3pnguyen/lionstride-inventeam-2026/Finalized Schematics/Finalized Pressure Schematic/Schematic Versions/Schematic V02/V2.2 - 5.3.2026/Pressure Schematic PCB.png

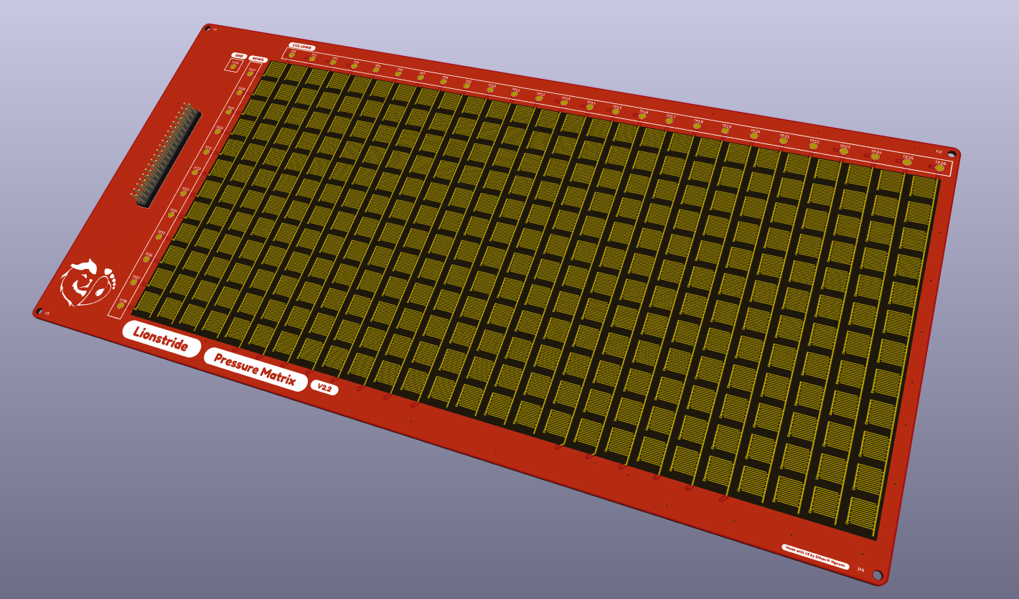
Finalized Schematics/Finalized Pressure Schematic/Schematic Versions/Schematic V02/V2.2 - 5.3.2026/Pressure Schematic PCB.png
