3pnguyen/lionstride-inventeam-2026/Finalized Schematics/Finalized Logic Schematic/Schematic Versions/Schematic V03/Logic Schematic.png

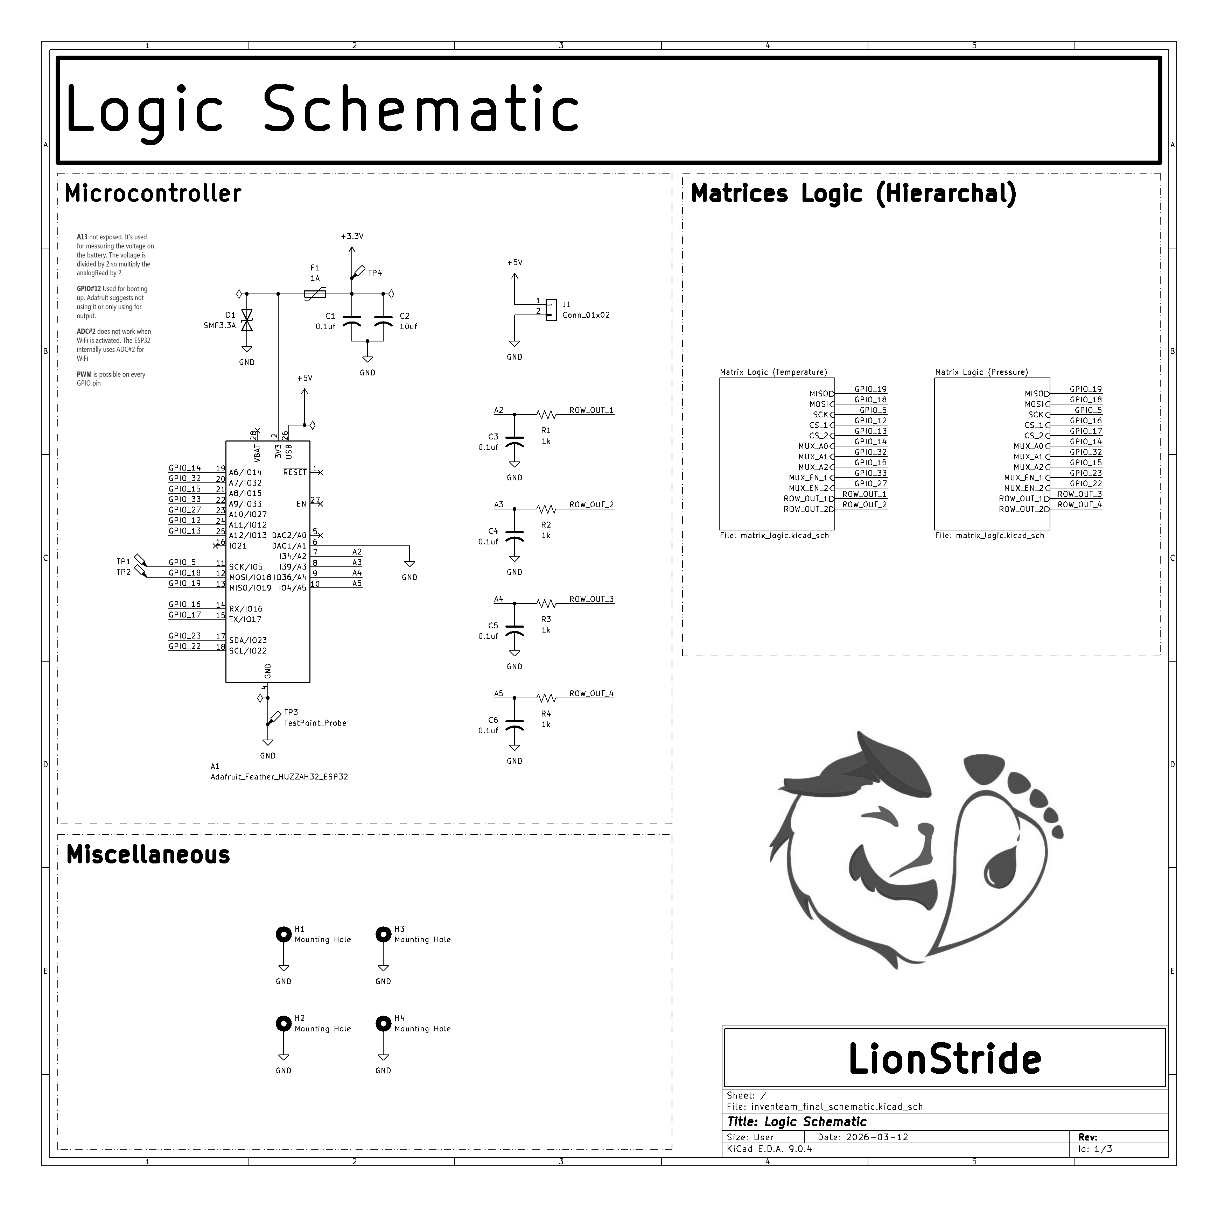
Finalized Schematics/Finalized Logic Schematic/Schematic Versions/Schematic V03/Logic Schematic.png
