3pnguyen/lionstride-inventeam-2026/Finalized Schematics/Finalized Logic Schematic/Schematic Versions/Schematic V03/Pressure Logic Subsheet.png

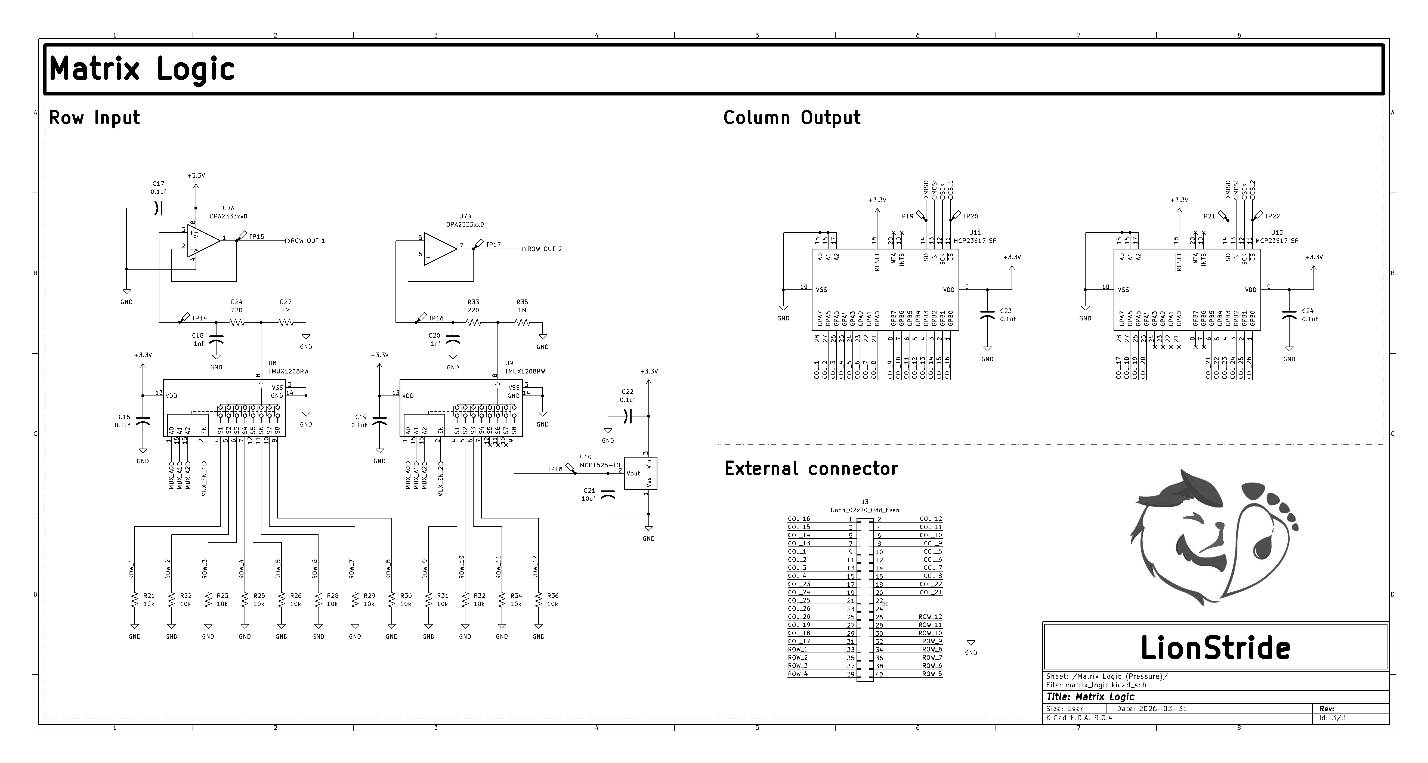
Finalized Schematics/Finalized Logic Schematic/Schematic Versions/Schematic V03/Pressure Logic Subsheet.png
