3pnguyen/lionstride-inventeam-2026/Finalized Schematics/Finalized Pressure Schematic/Schematic Versions/Schematic V02/Columns Hierarchical Schematic.png

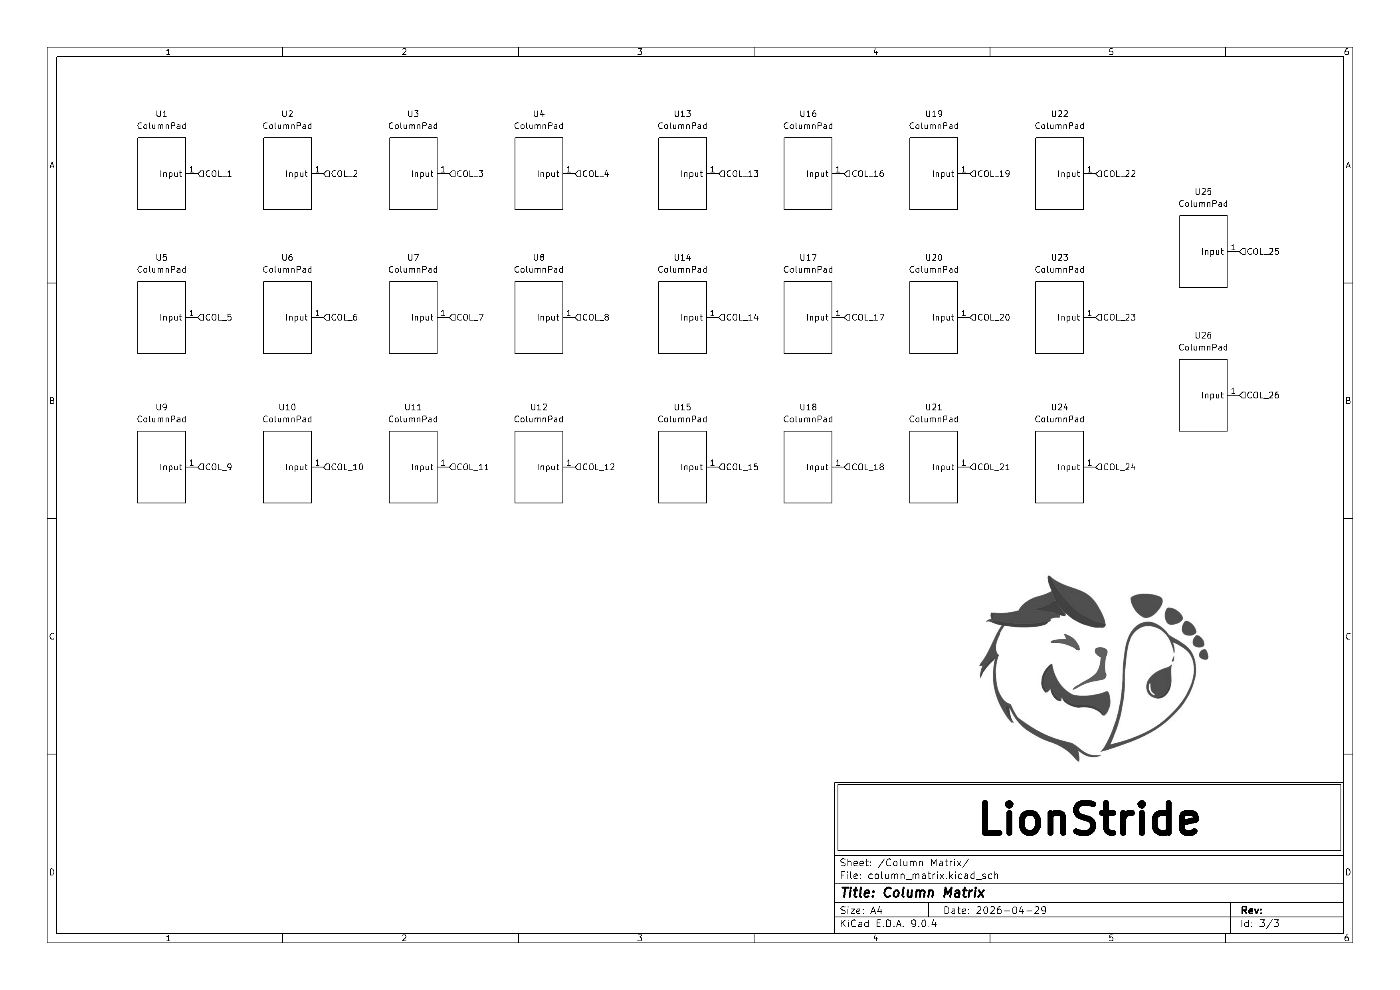
Finalized Schematics/Finalized Pressure Schematic/Schematic Versions/Schematic V02/Columns Hierarchical Schematic.png
