3pnguyen/lionstride-inventeam-2026/Finalized Schematics/Finalized Pressure Schematic/Schematic Versions/Schematic V02/V2.1 - 5.2.26/Pressure Schematic.png

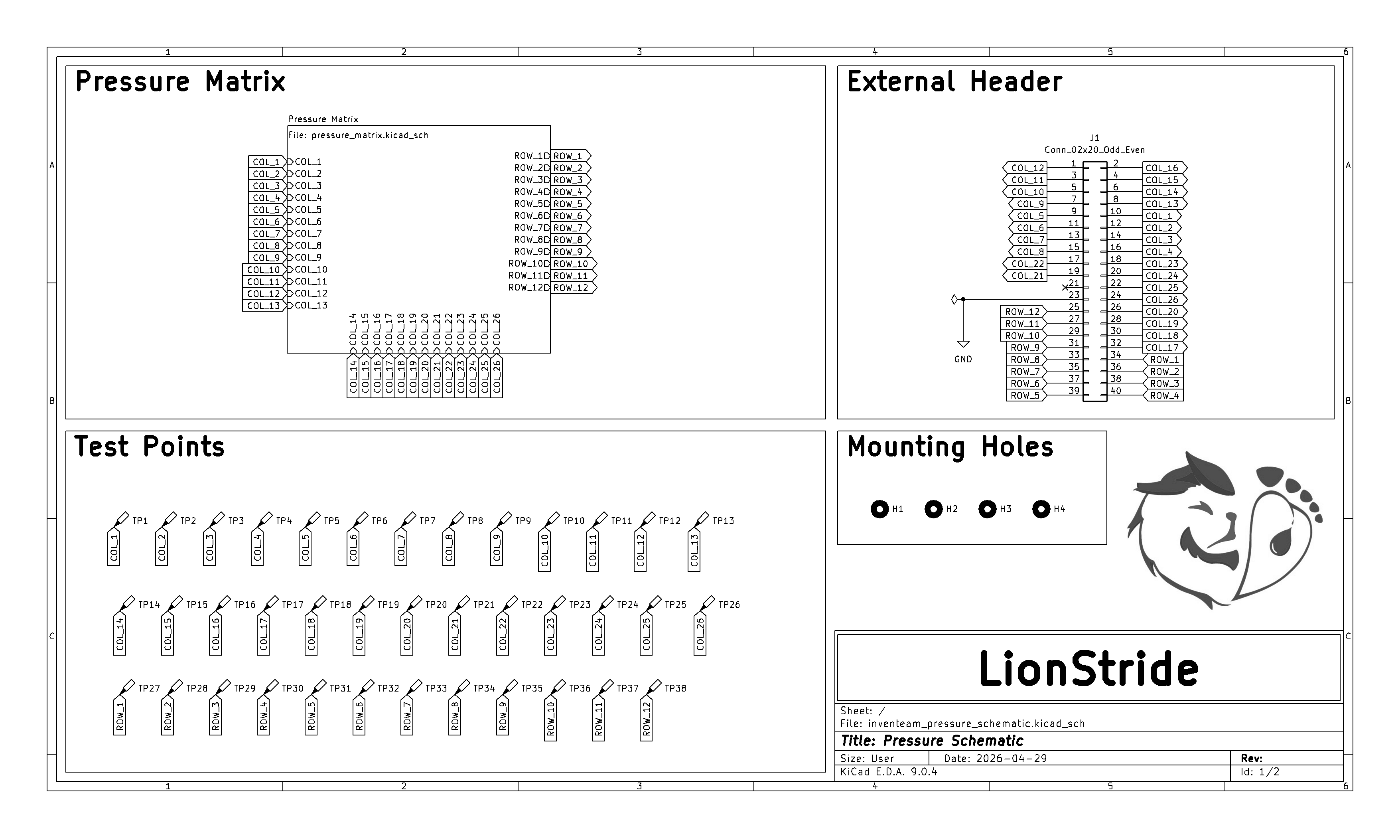
Finalized Schematics/Finalized Pressure Schematic/Schematic Versions/Schematic V02/V2.1 - 5.2.26/Pressure Schematic.png
