3pnguyen/lionstride-inventeam-2026/Finalized Schematics/Finalized Thermistor Schematic/Schematic Versions/Schematic V02/Matrix PCB Layout 2.png

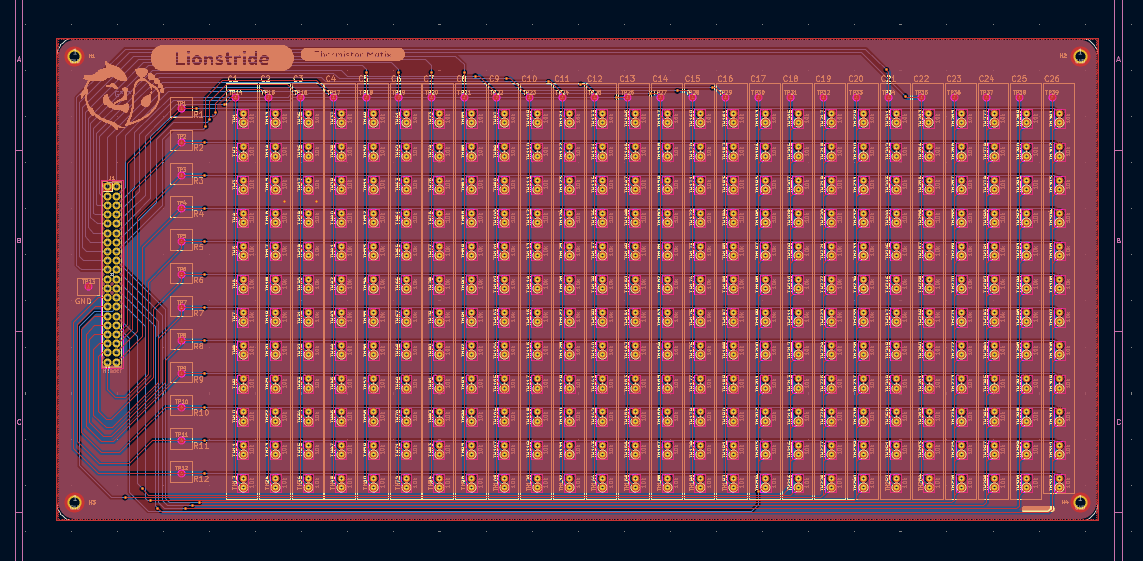
Finalized Schematics/Finalized Thermistor Schematic/Schematic Versions/Schematic V02/Matrix PCB Layout 2.png
