3pnguyen/lionstride-inventeam-2026/Finalized Schematics/Finalized Thermistor Schematic/Schematic Versions/Schematic V02/Thermistor Cell.png

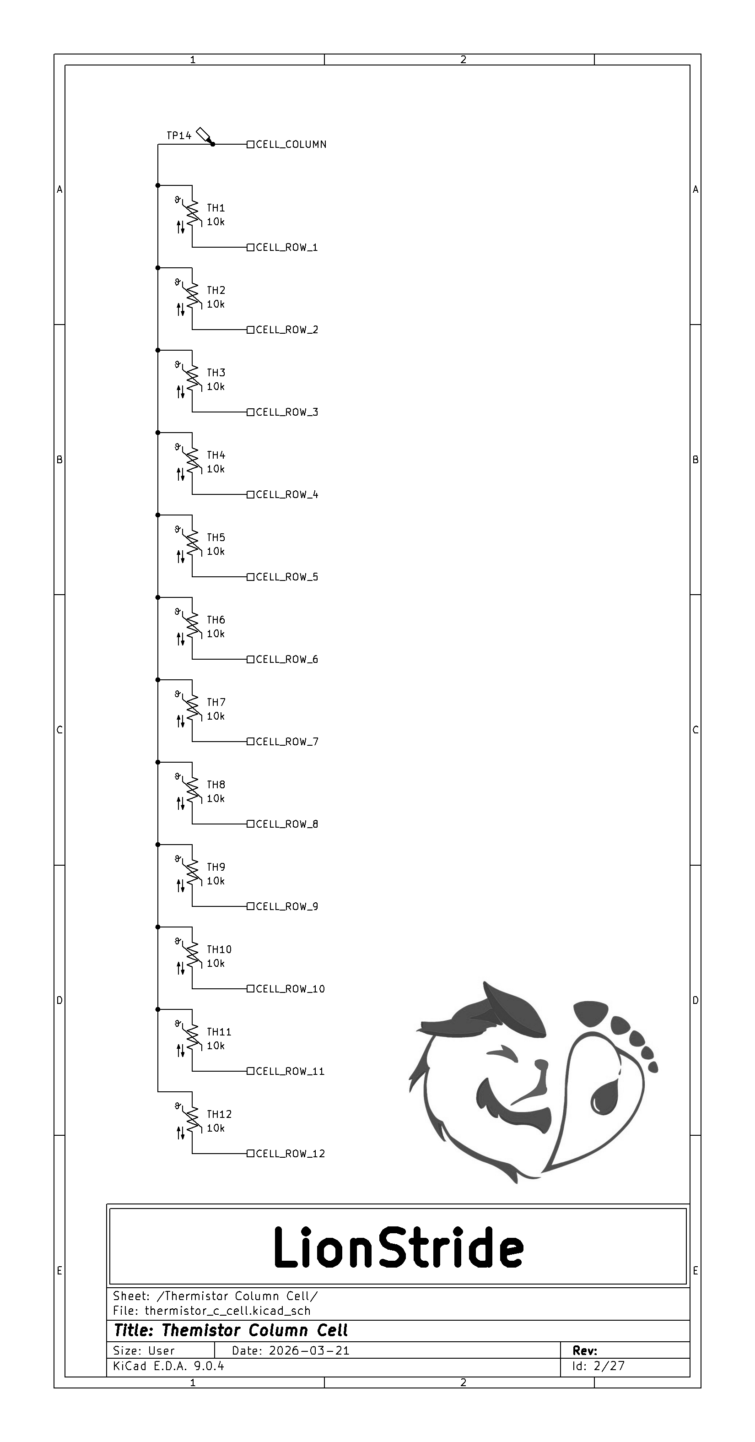
Finalized Schematics/Finalized Thermistor Schematic/Schematic Versions/Schematic V02/Thermistor Cell.png
