3pnguyen/lionstride-inventeam-2026/Finalized Schematics/Finalized Thermistor Schematic/Schematic Versions/Schematic V02/BOM.png

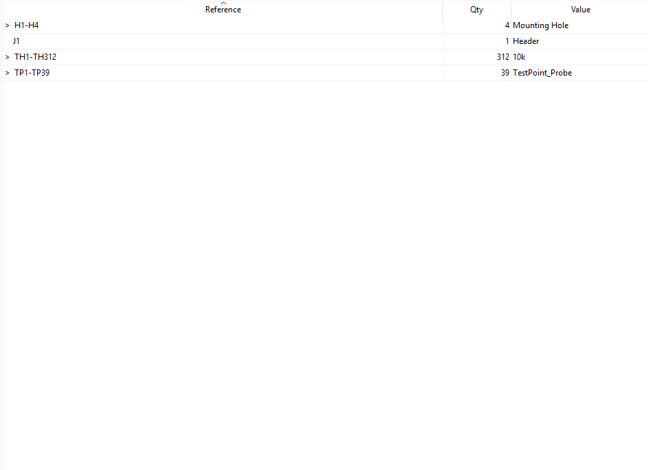
Finalized Schematics/Finalized Thermistor Schematic/Schematic Versions/Schematic V02/BOM.png
