3pnguyen/lionstride-inventeam-2026/Prototype Schematics/Prototype Schematic (VD)/Schematic Versions/Schematic V17/BOM.png

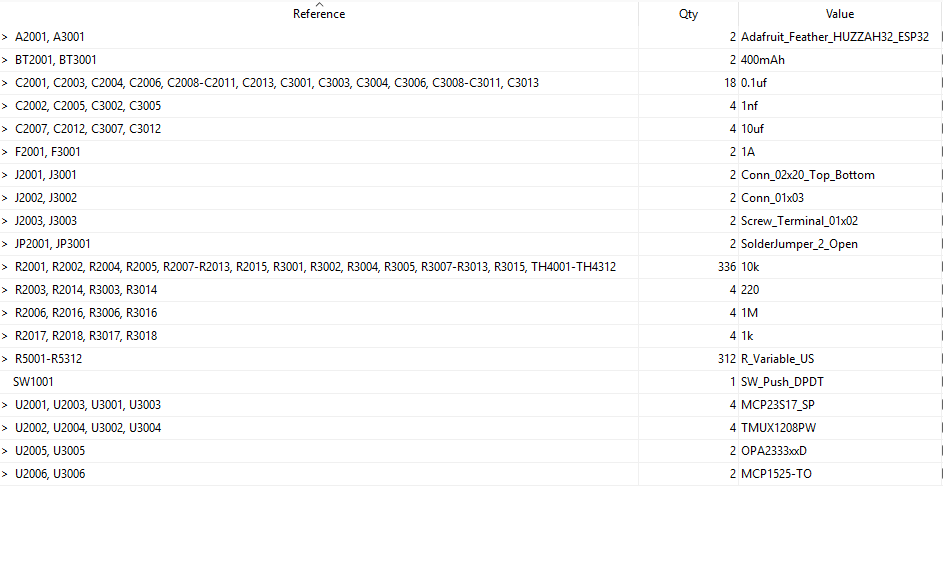
Prototype Schematics/Prototype Schematic (VD)/Schematic Versions/Schematic V17/BOM.png
