3pnguyen/lionstride-inventeam-2026/Prototype Schematics/inventeam_proto_schematics/Matrix_Columns.kicad_sch

## KiCad design Prototype Schematics/inventeam_proto_schematics/Matrix_Columns.kicad_sch (2026-02-23)

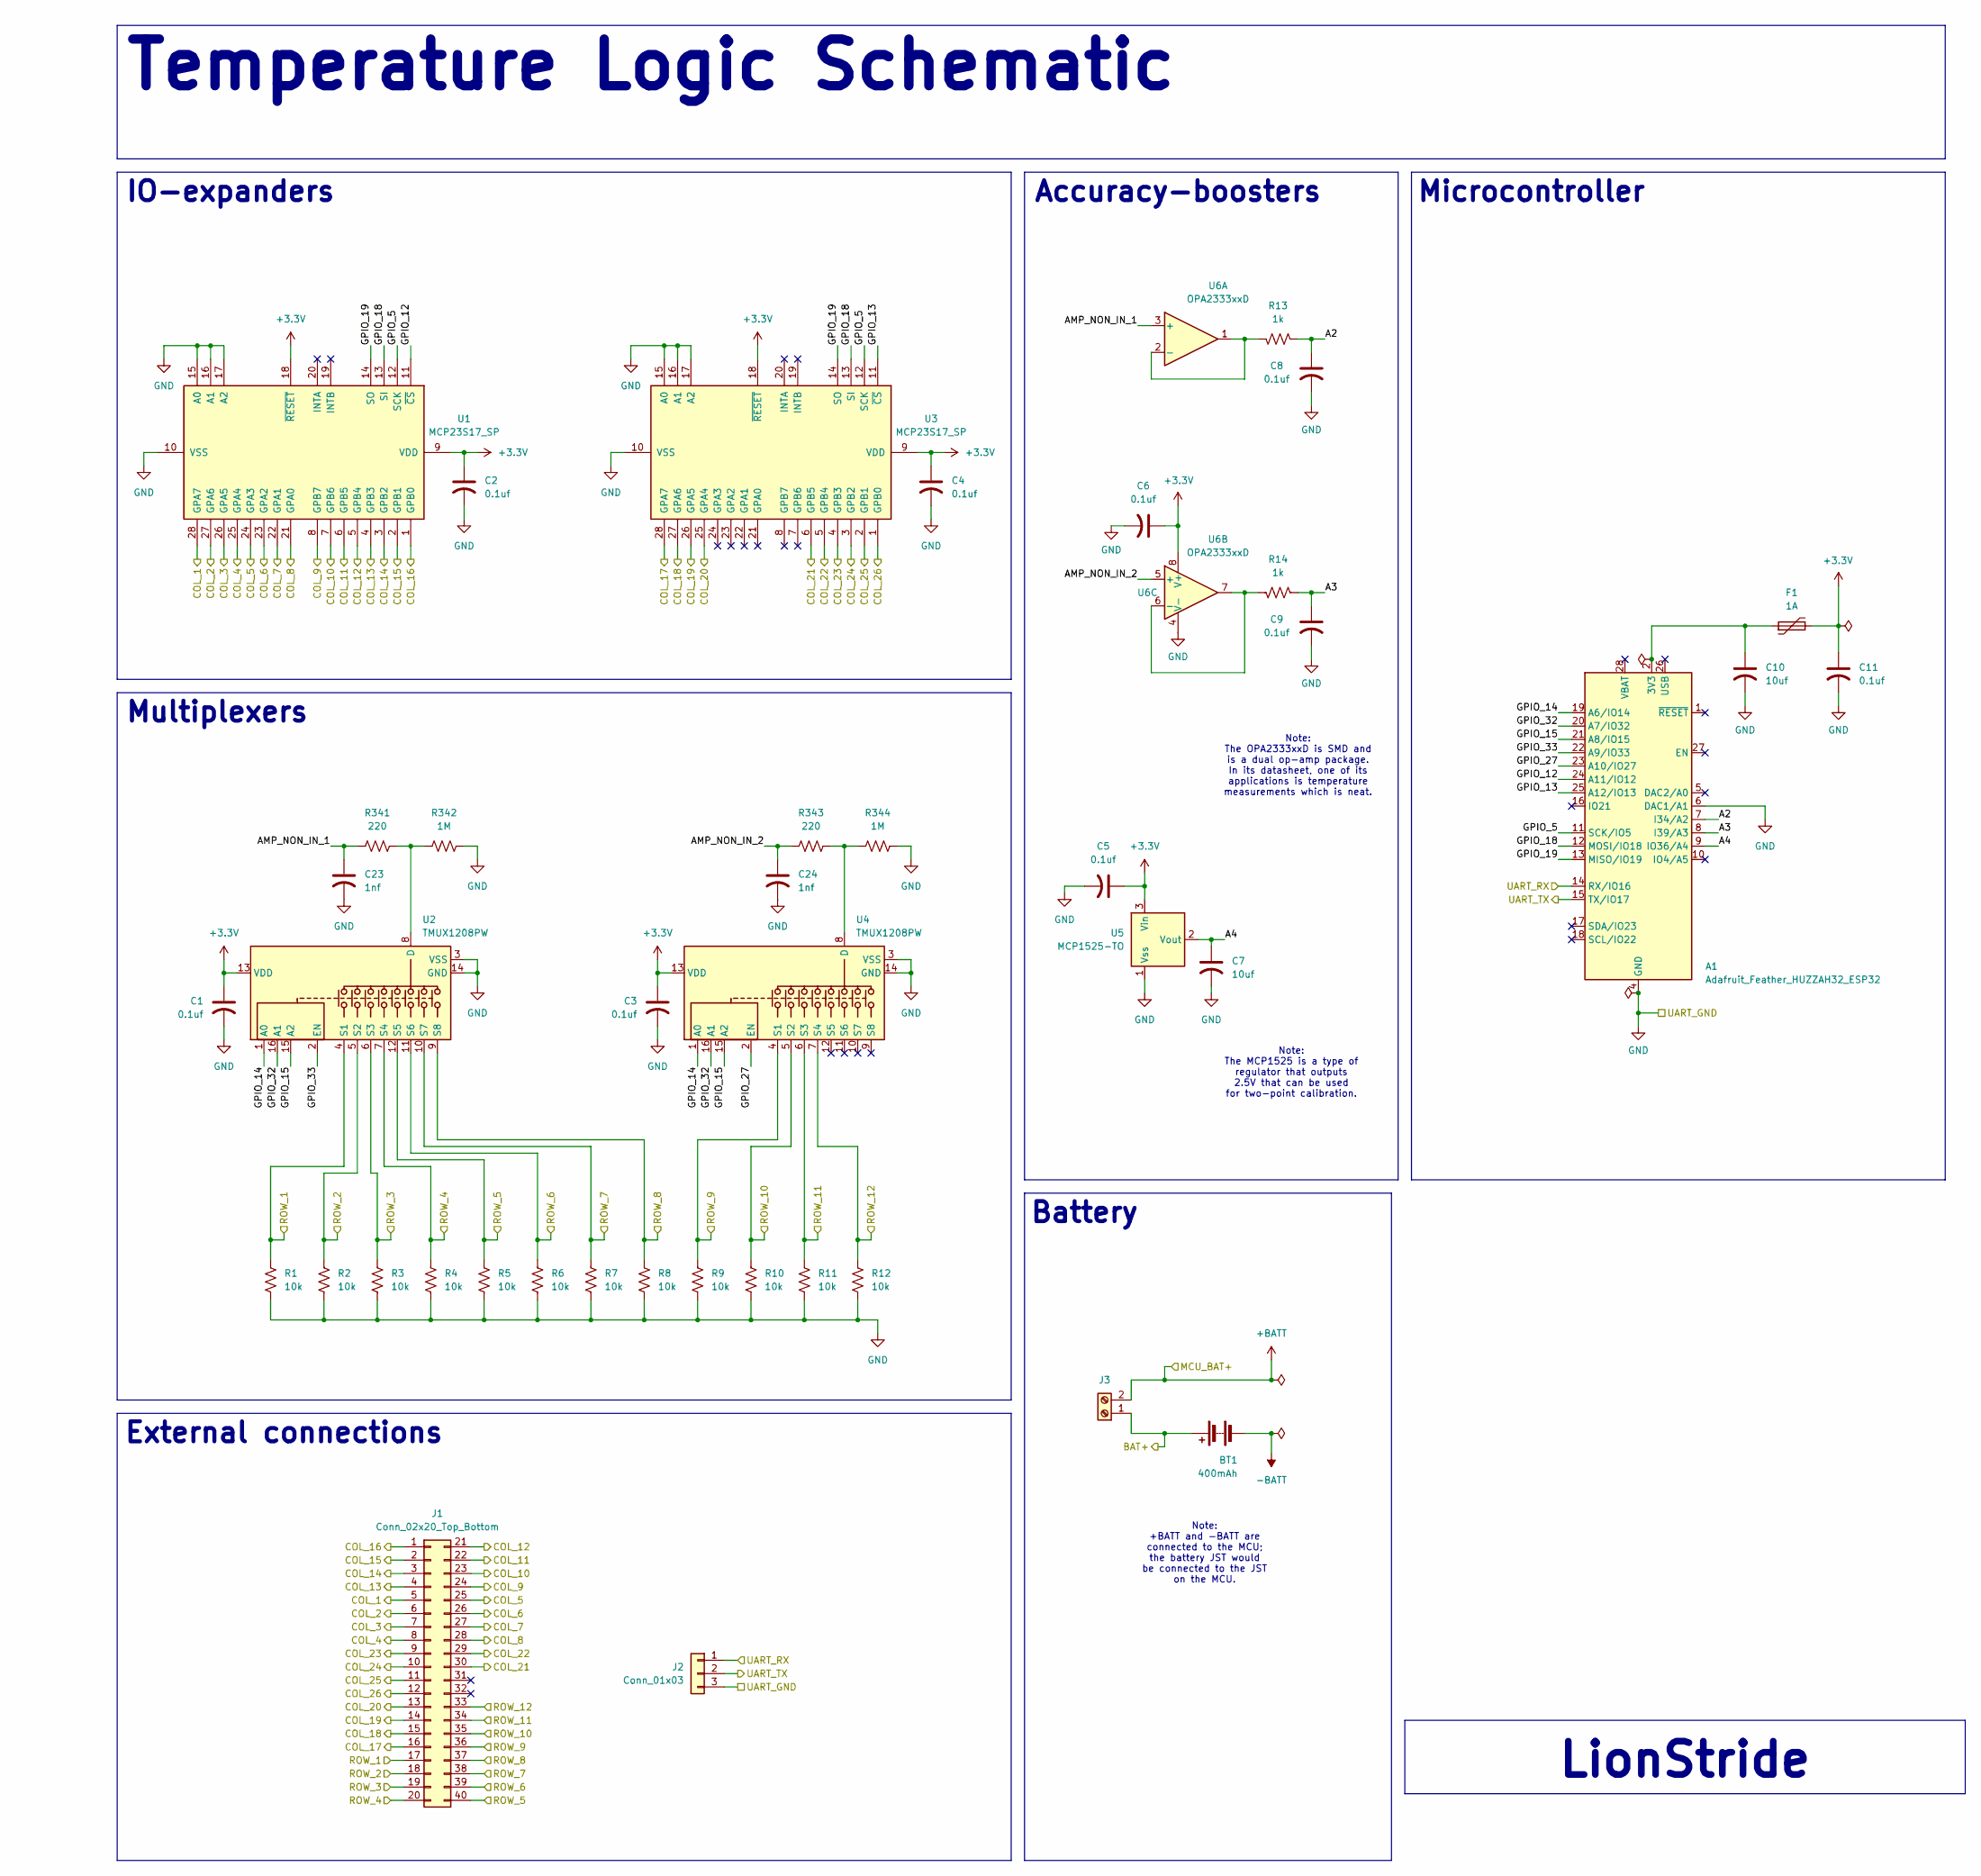
[picture p27: schematic Matrix_Columns.kicad_sch]

Parts:
A1: Adafruit_Feather_HUZZAH32_ESP32; Adafruit_Feather
BT1: 400mAh
C1, C2, C3, C4, C5, C6, C8, C9, C11: 0.1uf
C7, C10: 10uf
C23, C24: 1nf
F1: 1A
J1: Conn_02x20_Top_Bottom
J2: Conn_01x03
J3: Screw_Terminal_01x02
R1, R2, R3, R4, R5, R6, R7, R8, R9, R10, R11, R12: 10k
R13, R14: 1k
R341, R343: 220
R342, R344: 1M
U1, U3: MCP23S17_SP; DIP-28_W7.62mm
U2, U4: TMUX1208PW; TSSOP-16_4.4x5mm_P0.65mm
U5: MCP1525-TO; TO-92_Inline
U6: OPA2333xxD

Connections:
+3.3V: C1.1, C2.1, C3.1, C4.1, C5.1, C6.1, C11.1, F1.2, U1.9 (VDD), U1.18 (~RESET), U2.13 (VDD), U3.9 (VDD), U3.18 (~RESET), U4.13 (VDD), U5.3 (Vin), U6.8 (V+)
+BATT: J3.2
-BATT: BT1.2 (-)
A2: A1.7 (I34/A2), C8.1, R13.1
A3: A1.8 (I39/A3), C9.1, R14.2
A4: A1.9 (IO36/A4), C7.1, U5.2 (Vout)
AMP_NON_IN_1: C23.1, R341.2, U6.3 (+)
AMP_NON_IN_2: C24.1, R343.2, U6.5 (+)
BAT+: BT1.1 (+), J3.1
COL_1: J1.5, U1.28 (GPA7)
COL_2: J1.6, U1.27 (GPA6)
COL_3: J1.7, U1.26 (GPA5)
COL_4: J1.8, U1.25 (GPA4)
COL_5: J1.25, U1.24 (GPA3)
COL_6: J1.26, U1.23 (GPA2)
COL_7: J1.27, U1.22 (GPA1)
COL_8: J1.28, U1.21 (GPA0)
COL_9: J1.24, U1.8 (GPB7)
COL_10: J1.23, U1.7 (GPB6)
COL_11: J1.22, U1.6 (GPB5)
COL_12: J1.21, U1.5 (GPB4)
COL_13: J1.4, U1.4 (GPB3)
COL_14: J1.3, U1.3 (GPB2)
COL_15: J1.2, U1.2 (GPB1)
COL_16: J1.1, U1.1 (GPB0)
COL_17: J1.16, U3.28 (GPA7)
COL_18: J1.15, U3.27 (GPA6)
COL_19: J1.14, U3.26 (GPA5)
COL_20: J1.13, U3.25 (GPA4)
COL_21: J1.30, U3.6 (GPB5)
COL_22: J1.29, U3.5 (GPB4)
COL_23: J1.9, U3.4 (GPB3)
COL_24: J1.10, U3.3 (GPB2)
COL_25: J1.11, U3.2 (GPB1)
COL_26: J1.12, U3.1 (GPB0)
GND: A1.4 (GND), A1.6 (DAC1/A1), C1.2, C2.2, C3.2, C4.2, C5.2, C6.2, C7.2, C8.2, C9.2, C10.2, C11.2, C23.2, C24.2, J2.3, R1.2, R2.2, R3.2, R4.2, R5.2, R6.2, R7.2, R8.2, R9.2, R10.2, R11.2, R12.2, R342.2, R344.2, U1.10 (VSS), U1.15 (A0), U1.16 (A1), U1.17 (A2), U2.3 (VSS), U2.14 (GND), U3.10 (VSS), U3.15 (A0), U3.16 (A1), U3.17 (A2), U4.3 (VSS), U4.14 (GND), U5.1 (Vss), U6.4 (V-)
GPIO_5: A1.11 (SCK/IO5), U1.12 (SCK), U3.12 (SCK)
GPIO_12: A1.24 (A11/IO12), U1.11 (~CS)
GPIO_13: A1.25 (A12/IO13), U3.11 (~CS)
GPIO_14: A1.19 (A6/IO14), U2.1 (A0), U4.1 (A0)
GPIO_15: A1.21 (A8/IO15), U2.15 (A2), U4.15 (A2)
GPIO_18: A1.12 (MOSI/IO18), U1.13 (SI), U3.13 (SI)
GPIO_19: A1.13 (MISO/IO19), U1.14 (SO), U3.14 (SO)
GPIO_27: A1.23 (A10/IO27), U4.2 (EN)
GPIO_32: A1.20 (A7/IO32), U2.16 (A1), U4.16 (A1)
GPIO_33: A1.22 (A9/IO33), U2.2 (EN)
unnamed: A1.2 (3V3), C10.1, F1.1
unnamed: R13.2, U6.1, U6.2 (-)
unnamed: R14.1, U6.6 (-), U6.7
unnamed: R341.1, R342.1, U2.8 (D)
unnamed: R343.1, R344.1, U4.8 (D)
ROW_1: J1.17, R1.1, U2.4 (S1)
ROW_2: J1.18, R2.1, U2.5 (S2)
ROW_3: J1.19, R3.1, U2.6 (S3)
ROW_4: J1.20, R4.1, U2.7 (S4)
ROW_5: J1.40, R5.1, U2.12 (S5)
ROW_6: J1.39, R6.1, U2.11 (S6)
ROW_7: J1.38, R7.1, U2.10 (S7)
ROW_8: J1.37, R8.1, U2.9 (S8)
ROW_9: J1.36, R9.1, U4.4 (S1)
ROW_10: J1.35, R10.1, U4.5 (S2)
ROW_11: J1.34, R11.1, U4.6 (S3)
ROW_12: J1.33, R12.1, U4.7 (S4)
UART_RX: A1.14 (RX/IO16), J2.1
UART_TX: A1.15 (TX/IO17), J2.2

Notes on the sheet:
Battery
Temperature Logic Schematic
Note: The OPA2333xxD is SMD and is a dual op-amp package. In its datasheet, one of its applications is temperature measurements which is neat.
Note: The MCP1525 is a type of regulator that outputs 2.5V that can be used for two-point calibration.
Note: +BATT and -BATT are connected to the MCU; the battery JST would be connected to the JST on the MCU.
LionStride
Microcontroller
Multiplexers
IO-expanders
Accuracy-boosters
External connections
