3pnguyen/lionstride-inventeam-2026/Prototype Schematics/Prototype Schematic (TIA)/inventeam_proto_schematics_tia/FSR Matrix Schematic.kicad_sch

## KiCad design Prototype Schematics/Prototype Schematic (TIA)/inventeam_proto_schematics_tia/FSR Matrix Schematic.kicad_sch (2026-03-04)

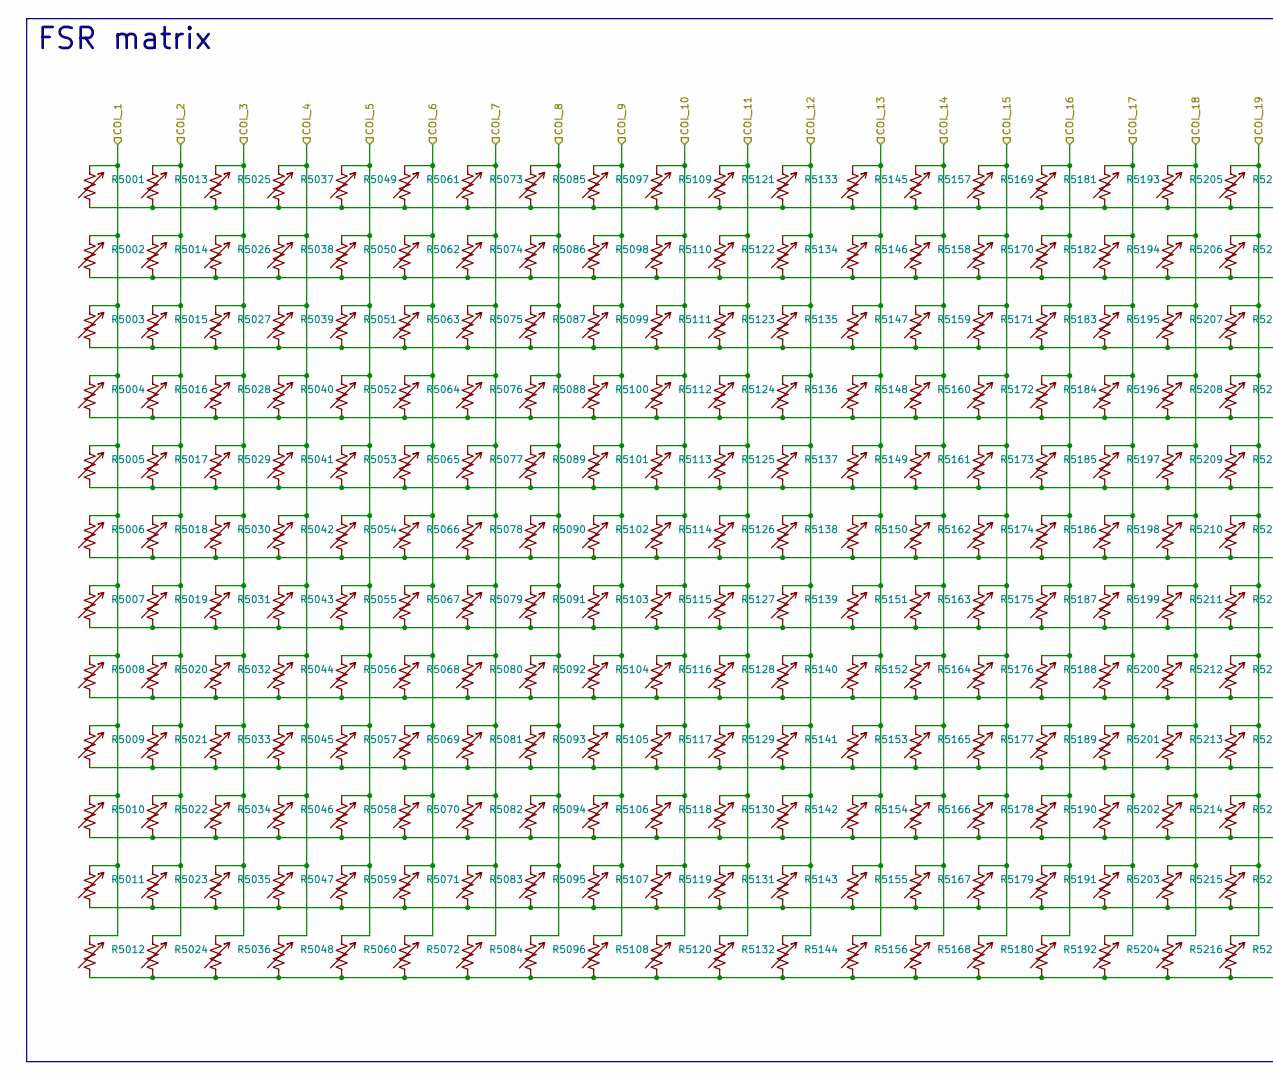
[picture p30: schematic FSR Matrix Schematic.kicad_sch, part in row 1, column 1]

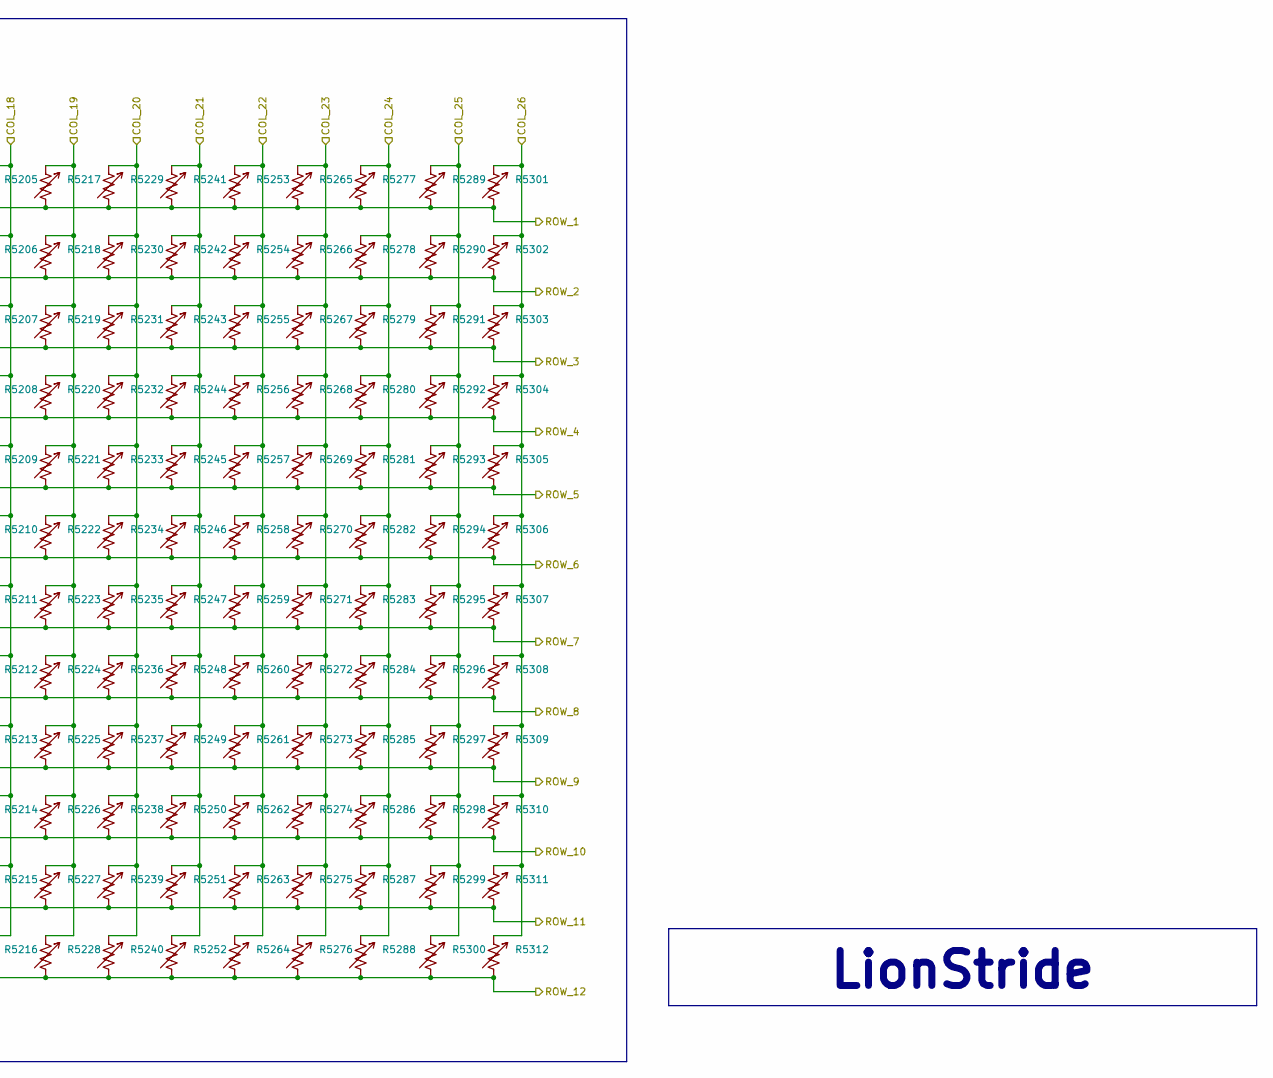
[picture p31: schematic FSR Matrix Schematic.kicad_sch, part in row 1, column 2]

Parts:
R5001, R5002, R5003, R5004, R5005, R5006, R5007, R5008, R5009, R5010, R5011, R5012, R5013, R5014, R5015, R5016, R5017, R5018, R5019, R5020, R5021, R5022, R5023, R5024, R5025, R5026, R5027, R5028, R5029, R5030, R5031, R5032, R5033, R5034, R5035, R5036, R5037, R5038, R5039, R5040, R5041, R5042, R5043, R5044, R5045, R5046, R5047, R5048, R5049, R5050, R5051, R5052, R5053, R5054, R5055, R5056, R5057, R5058, R5059, R5060, R5061, R5062, R5063, R5064, R5065, R5066, R5067, R5068, R5069, R5070, R5071, R5072, R5073, R5074, R5075, R5076, R5077, R5078, R5079, R5080, R5081, R5082, R5083, R5084, R5085, R5086, R5087, R5088, R5089, R5090, R5091, R5092, R5093, R5094, R5095, R5096, R5097, R5098, R5099, R5100, R5101, R5102, R5103, R5104, R5105, R5106, R5107, R5108, R5109, R5110, R5111, R5112, R5113, R5114, R5115, R5116, R5117, R5118, R5119, R5120, R5121, R5122, R5123, R5124, R5125, R5126, R5127, R5128, R5129, R5130, R5131, R5132, R5133, R5134, R5135, R5136, R5137, R5138, R5139, R5140, R5141, R5142, R5143, R5144, R5145, R5146, R5147, R5148, R5149, R5150, R5151, R5152, R5153, R5154, R5155, R5156, R5157, R5158, R5159, R5160, R5161, R5162, R5163, R5164, R5165, R5166, R5167, R5168, R5169, R5170, R5171, R5172, R5173, R5174, R5175, R5176, R5177, R5178, R5179, R5180, R5181, R5182, R5183, R5184, R5185, R5186, R5187, R5188, R5189, R5190, R5191, R5192, R5193, R5194, R5195, R5196, R5197, R5198, R5199, R5200, R5201, R5202, R5203, R5204, R5205, R5206, R5207, R5208, R5209, R5210, R5211, R5212, R5213, R5214, R5215, R5216, R5217, R5218, R5219, R5220, R5221, R5222, R5223, R5224, R5225, R5226, R5227, R5228, R5229, R5230, R5231, R5232, R5233, R5234, R5235, R5236, R5237, R5238, R5239, R5240, R5241, R5242, R5243, R5244, R5245, R5246, R5247, R5248, R5249, R5250, R5251, R5252, R5253, R5254, R5255, R5256, R5257, R5258, R5259, R5260, R5261, R5262, R5263, R5264, R5265, R5266, R5267, R5268, R5269, R5270, R5271, R5272, R5273, R5274, R5275, R5276, R5277, R5278, R5279, R5280, R5281, R5282, R5283, R5284, R5285, R5286, R5287, R5288, R5289, R5290, R5291, R5292, R5293, R5294, R5295, R5296, R5297, R5298, R5299, R5300, R5301, R5302, R5303, R5304, R5305, R5306, R5307, R5308, R5309, R5310, R5311, R5312: R_Variable_US

Connections:
COL_1: R5001.1, R5002.1, R5003.1, R5004.1, R5005.1, R5006.1, R5007.1, R5008.1, R5009.1, R5010.1, R5011.1, R5012.1
COL_2: R5013.1, R5014.1, R5015.1, R5016.1, R5017.1, R5018.1, R5019.1, R5020.1, R5021.1, R5022.1, R5023.1, R5024.1
COL_3: R5025.1, R5026.1, R5027.1, R5028.1, R5029.1, R5030.1, R5031.1, R5032.1, R5033.1, R5034.1, R5035.1, R5036.1
COL_4: R5037.1, R5038.1, R5039.1, R5040.1, R5041.1, R5042.1, R5043.1, R5044.1, R5045.1, R5046.1, R5047.1, R5048.1
COL_5: R5049.1, R5050.1, R5051.1, R5052.1, R5053.1, R5054.1, R5055.1, R5056.1, R5057.1, R5058.1, R5059.1, R5060.1
COL_6: R5061.1, R5062.1, R5063.1, R5064.1, R5065.1, R5066.1, R5067.1, R5068.1, R5069.1, R5070.1, R5071.1, R5072.1
COL_7: R5073.1, R5074.1, R5075.1, R5076.1, R5077.1, R5078.1, R5079.1, R5080.1, R5081.1, R5082.1, R5083.1, R5084.1
COL_8: R5085.1, R5086.1, R5087.1, R5088.1, R5089.1, R5090.1, R5091.1, R5092.1, R5093.1, R5094.1, R5095.1, R5096.1
COL_9: R5097.1, R5098.1, R5099.1, R5100.1, R5101.1, R5102.1, R5103.1, R5104.1, R5105.1, R5106.1, R5107.1, R5108.1
COL_10: R5109.1, R5110.1, R5111.1, R5112.1, R5113.1, R5114.1, R5115.1, R5116.1, R5117.1, R5118.1, R5119.1, R5120.1
COL_11: R5121.1, R5122.1, R5123.1, R5124.1, R5125.1, R5126.1, R5127.1, R5128.1, R5129.1, R5130.1, R5131.1, R5132.1
COL_12: R5133.1, R5134.1, R5135.1, R5136.1, R5137.1, R5138.1, R5139.1, R5140.1, R5141.1, R5142.1, R5143.1, R5144.1
COL_13: R5145.1, R5146.1, R5147.1, R5148.1, R5149.1, R5150.1, R5151.1, R5152.1, R5153.1, R5154.1, R5155.1, R5156.1
COL_14: R5157.1, R5158.1, R5159.1, R5160.1, R5161.1, R5162.1, R5163.1, R5164.1, R5165.1, R5166.1, R5167.1, R5168.1
COL_15: R5169.1, R5170.1, R5171.1, R5172.1, R5173.1, R5174.1, R5175.1, R5176.1, R5177.1, R5178.1, R5179.1, R5180.1
COL_16: R5181.1, R5182.1, R5183.1, R5184.1, R5185.1, R5186.1, R5187.1, R5188.1, R5189.1, R5190.1, R5191.1, R5192.1
COL_17: R5193.1, R5194.1, R5195.1, R5196.1, R5197.1, R5198.1, R5199.1, R5200.1, R5201.1, R5202.1, R5203.1, R5204.1
COL_18: R5205.1, R5206.1, R5207.1, R5208.1, R5209.1, R5210.1, R5211.1, R5212.1, R5213.1, R5214.1, R5215.1, R5216.1
COL_19: R5217.1, R5218.1, R5219.1, R5220.1, R5221.1, R5222.1, R5223.1, R5224.1, R5225.1, R5226.1, R5227.1, R5228.1
COL_20: R5229.1, R5230.1, R5231.1, R5232.1, R5233.1, R5234.1, R5235.1, R5236.1, R5237.1, R5238.1, R5239.1, R5240.1
COL_21: R5241.1, R5242.1, R5243.1, R5244.1, R5245.1, R5246.1, R5247.1, R5248.1, R5249.1, R5250.1, R5251.1, R5252.1
COL_22: R5253.1, R5254.1, R5255.1, R5256.1, R5257.1, R5258.1, R5259.1, R5260.1, R5261.1, R5262.1, R5263.1, R5264.1
COL_23: R5265.1, R5266.1, R5267.1, R5268.1, R5269.1, R5270.1, R5271.1, R5272.1, R5273.1, R5274.1, R5275.1, R5276.1
COL_24: R5277.1, R5278.1, R5279.1, R5280.1, R5281.1, R5282.1, R5283.1, R5284.1, R5285.1, R5286.1, R5287.1, R5288.1
COL_25: R5289.1, R5290.1, R5291.1, R5292.1, R5293.1, R5294.1, R5295.1, R5296.1, R5297.1, R5298.1, R5299.1, R5300.1
COL_26: R5301.1, R5302.1, R5303.1, R5304.1, R5305.1, R5306.1, R5307.1, R5308.1, R5309.1, R5310.1, R5311.1, R5312.1
ROW_1: R5001.2, R5013.2, R5025.2, R5037.2, R5049.2, R5061.2, R5073.2, R5085.2, R5097.2, R5109.2, R5121.2, R5133.2, R5145.2, R5157.2, R5169.2, R5181.2, R5193.2, R5205.2, R5217.2, R5229.2, R5241.2, R5253.2, R5265.2, R5277.2, R5289.2, R5301.2
ROW_2: R5002.2, R5014.2, R5026.2, R5038.2, R5050.2, R5062.2, R5074.2, R5086.2, R5098.2, R5110.2, R5122.2, R5134.2, R5146.2, R5158.2, R5170.2, R5182.2, R5194.2, R5206.2, R5218.2, R5230.2, R5242.2, R5254.2, R5266.2, R5278.2, R5290.2, R5302.2
ROW_3: R5003.2, R5015.2, R5027.2, R5039.2, R5051.2, R5063.2, R5075.2, R5087.2, R5099.2, R5111.2, R5123.2, R5135.2, R5147.2, R5159.2, R5171.2, R5183.2, R5195.2, R5207.2, R5219.2, R5231.2, R5243.2, R5255.2, R5267.2, R5279.2, R5291.2, R5303.2
ROW_4: R5004.2, R5016.2, R5028.2, R5040.2, R5052.2, R5064.2, R5076.2, R5088.2, R5100.2, R5112.2, R5124.2, R5136.2, R5148.2, R5160.2, R5172.2, R5184.2, R5196.2, R5208.2, R5220.2, R5232.2, R5244.2, R5256.2, R5268.2, R5280.2, R5292.2, R5304.2
ROW_5: R5005.2, R5017.2, R5029.2, R5041.2, R5053.2, R5065.2, R5077.2, R5089.2, R5101.2, R5113.2, R5125.2, R5137.2, R5149.2, R5161.2, R5173.2, R5185.2, R5197.2, R5209.2, R5221.2, R5233.2, R5245.2, R5257.2, R5269.2, R5281.2, R5293.2, R5305.2
ROW_6: R5006.2, R5018.2, R5030.2, R5042.2, R5054.2, R5066.2, R5078.2, R5090.2, R5102.2, R5114.2, R5126.2, R5138.2, R5150.2, R5162.2, R5174.2, R5186.2, R5198.2, R5210.2, R5222.2, R5234.2, R5246.2, R5258.2, R5270.2, R5282.2, R5294.2, R5306.2
ROW_7: R5007.2, R5019.2, R5031.2, R5043.2, R5055.2, R5067.2, R5079.2, R5091.2, R5103.2, R5115.2, R5127.2, R5139.2, R5151.2, R5163.2, R5175.2, R5187.2, R5199.2, R5211.2, R5223.2, R5235.2, R5247.2, R5259.2, R5271.2, R5283.2, R5295.2, R5307.2
ROW_8: R5008.2, R5020.2, R5032.2, R5044.2, R5056.2, R5068.2, R5080.2, R5092.2, R5104.2, R5116.2, R5128.2, R5140.2, R5152.2, R5164.2, R5176.2, R5188.2, R5200.2, R5212.2, R5224.2, R5236.2, R5248.2, R5260.2, R5272.2, R5284.2, R5296.2, R5308.2
ROW_9: R5009.2, R5021.2, R5033.2, R5045.2, R5057.2, R5069.2, R5081.2, R5093.2, R5105.2, R5117.2, R5129.2, R5141.2, R5153.2, R5165.2, R5177.2, R5189.2, R5201.2, R5213.2, R5225.2, R5237.2, R5249.2, R5261.2, R5273.2, R5285.2, R5297.2, R5309.2
ROW_10: R5010.2, R5022.2, R5034.2, R5046.2, R5058.2, R5070.2, R5082.2, R5094.2, R5106.2, R5118.2, R5130.2, R5142.2, R5154.2, R5166.2, R5178.2, R5190.2, R5202.2, R5214.2, R5226.2, R5238.2, R5250.2, R5262.2, R5274.2, R5286.2, R5298.2, R5310.2
ROW_11: R5011.2, R5023.2, R5035.2, R5047.2, R5059.2, R5071.2, R5083.2, R5095.2, R5107.2, R5119.2, R5131.2, R5143.2, R5155.2, R5167.2, R5179.2, R5191.2, R5203.2, R5215.2, R5227.2, R5239.2, R5251.2, R5263.2, R5275.2, R5287.2, R5299.2, R5311.2
ROW_12: R5012.2, R5024.2, R5036.2, R5048.2, R5060.2, R5072.2, R5084.2, R5096.2, R5108.2, R5120.2, R5132.2, R5144.2, R5156.2, R5168.2, R5180.2, R5192.2, R5204.2, R5216.2, R5228.2, R5240.2, R5252.2, R5264.2, R5276.2, R5288.2, R5300.2, R5312.2

Notes on the sheet:
LionStride
FSR matrix
