3pnguyen/lionstride-inventeam-2026/Prototype Schematics/Prototype Schematic (TIA)/inventeam_proto_schematics_tia/Logic Schematic.kicad_sch

## KiCad design Prototype Schematics/Prototype Schematic (TIA)/inventeam_proto_schematics_tia/Logic Schematic.kicad_sch (2026-03-20)

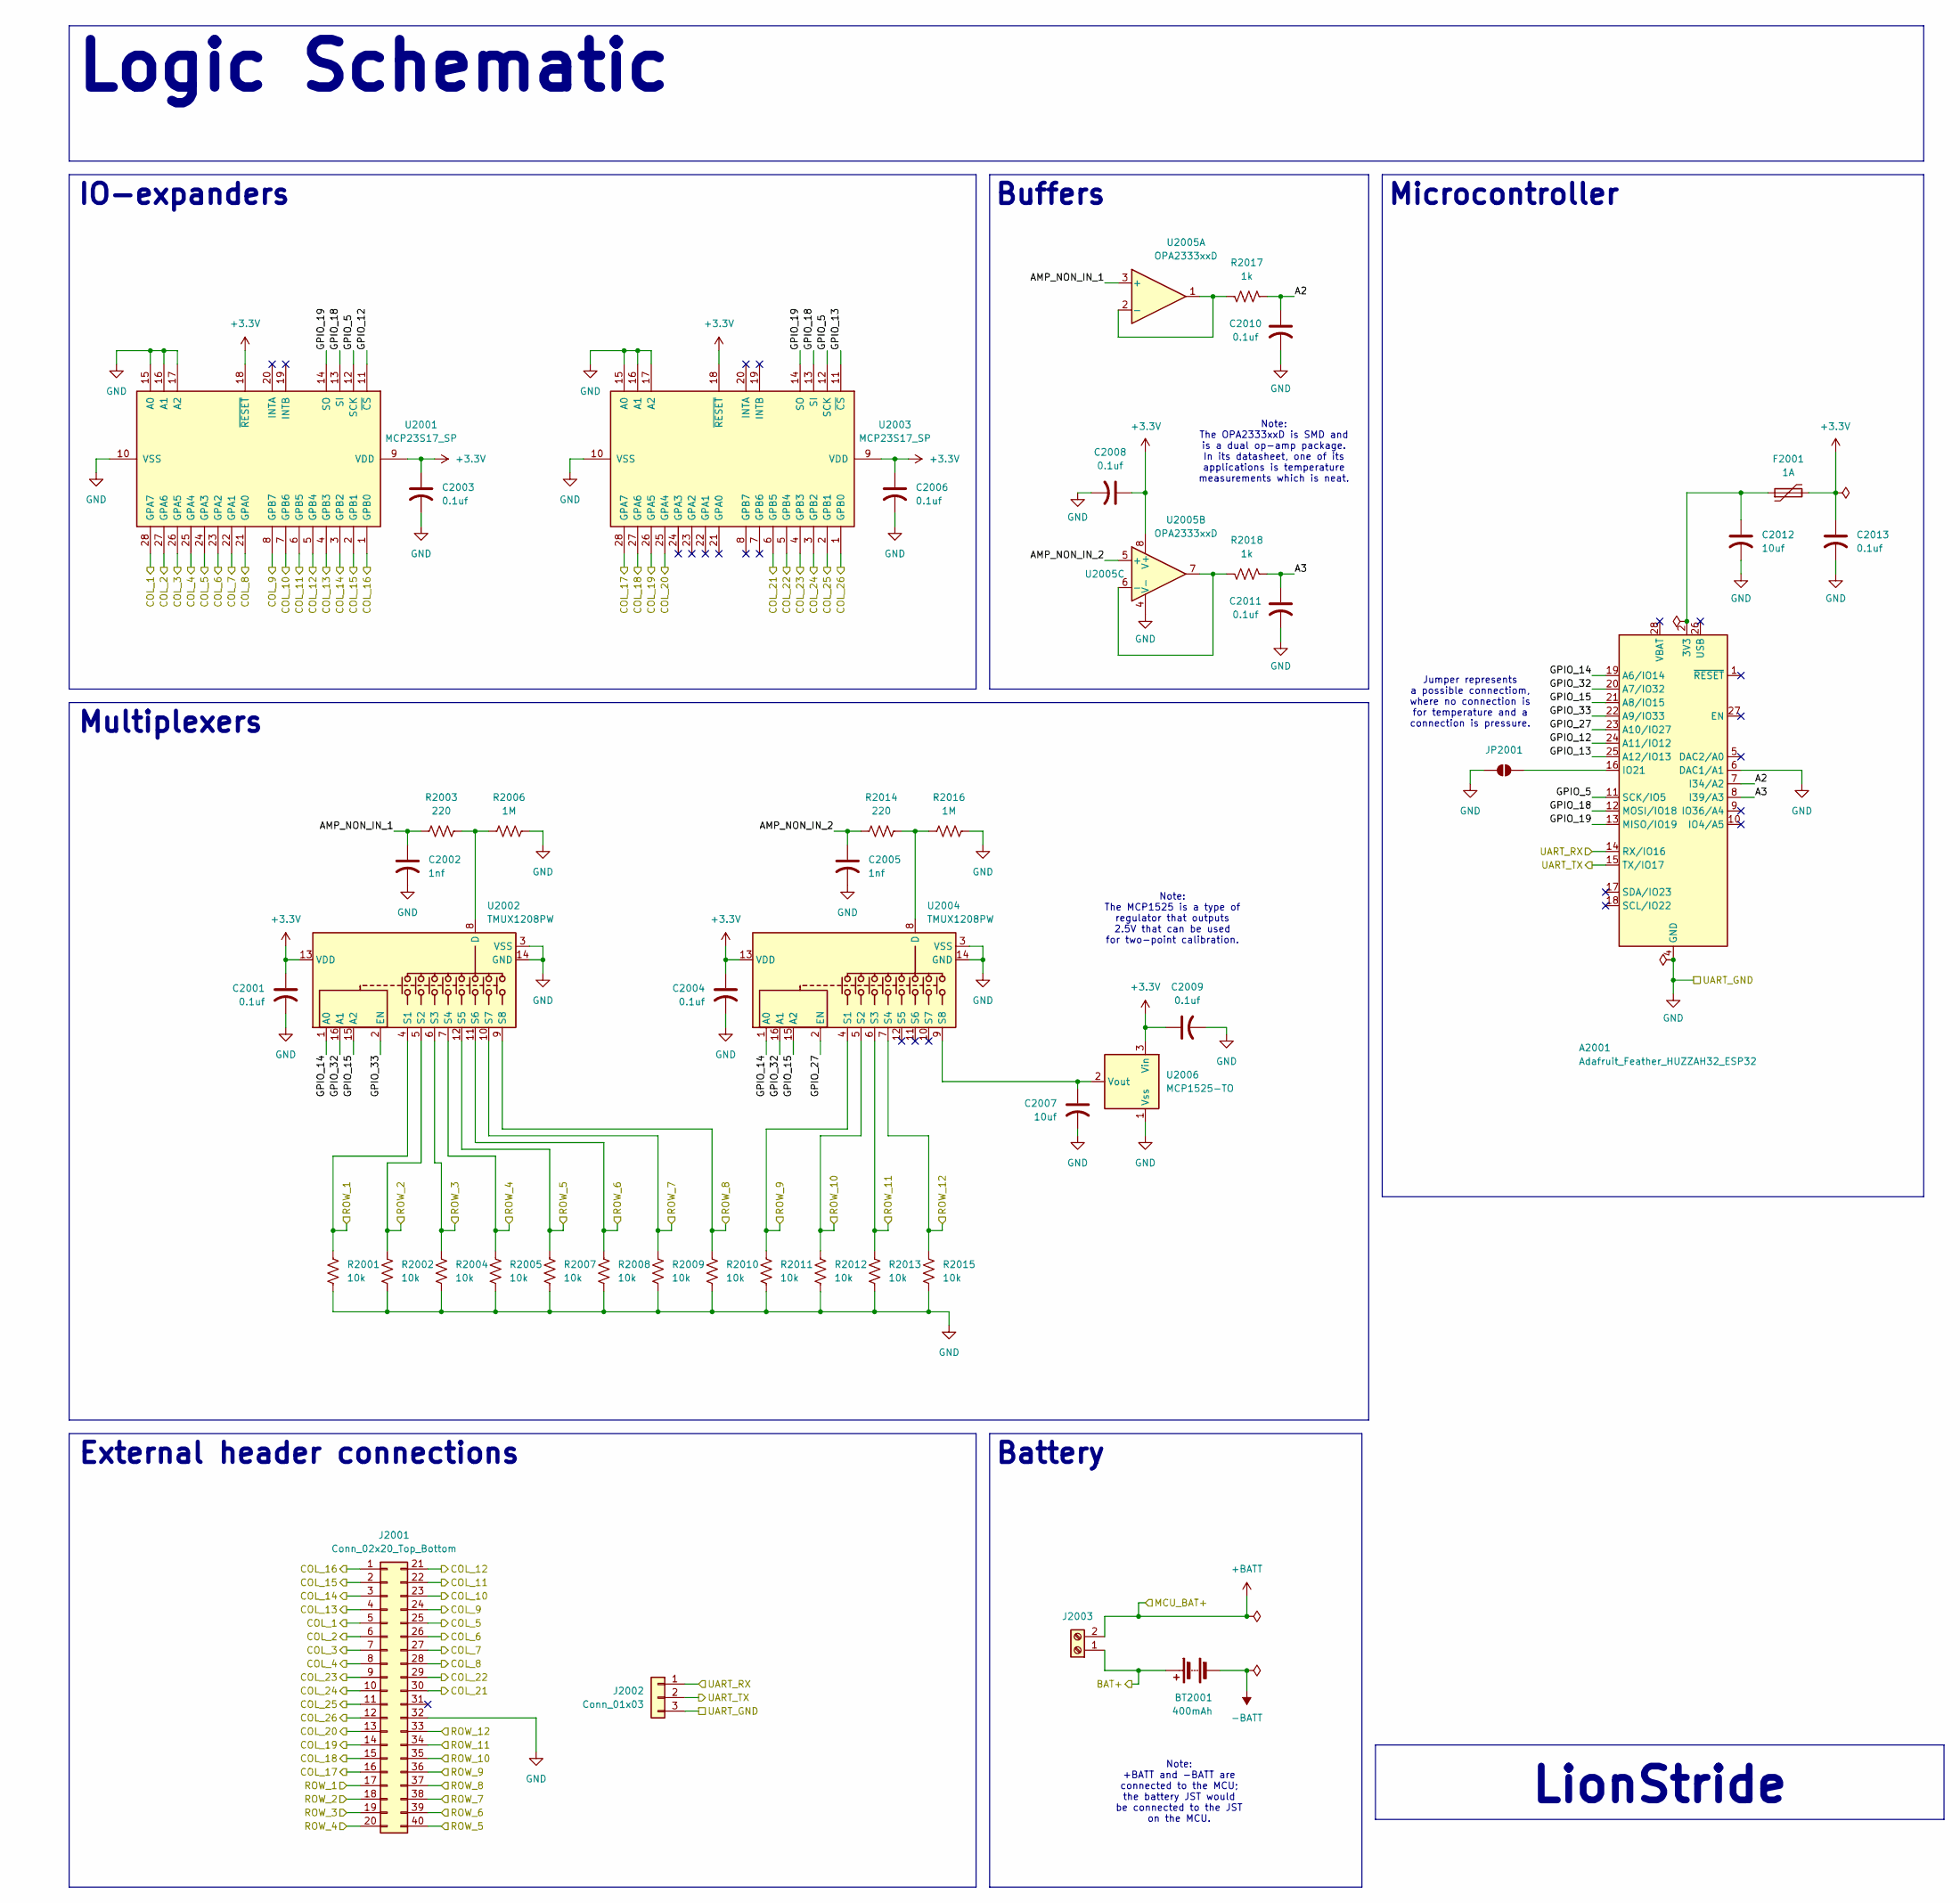
[picture p32: schematic Logic Schematic.kicad_sch]

Parts:
A2001: Adafruit_Feather_HUZZAH32_ESP32; Adafruit_Feather
BT2001: 400mAh
C2001, C2003, C2004, C2006, C2008, C2009, C2010, C2011, C2013: 0.1uf
C2002, C2005: 1nf
C2007, C2012: 10uf
F2001: 1A
J2001: Conn_02x20_Top_Bottom
J2002: Conn_01x03
J2003: Screw_Terminal_01x02
JP2001: SolderJumper_2_Open
R2001, R2002, R2004, R2005, R2007, R2008, R2009, R2010, R2011, R2012, R2013, R2015: 10k
R2003, R2014: 220
R2006, R2016: 1M
R2017, R2018: 1k
U2001, U2003: MCP23S17_SP; DIP-28_W7.62mm
U2002, U2004: TMUX1208PW; TSSOP-16_4.4x5mm_P0.65mm
U2005: OPA2333xxD
U2006: MCP1525-TO; TO-92_Inline

Connections:
+3.3V: C2001.1, C2003.1, C2004.1, C2006.1, C2008.1, C2009.1, C2013.1, F2001.2, U2001.9 (VDD), U2001.18 (~RESET), U2002.13 (VDD), U2003.9 (VDD), U2003.18 (~RESET), U2004.13 (VDD), U2005.8 (V+), U2006.3 (Vin)
+BATT: J2003.2
-BATT: BT2001.2 (-)
A2: A2001.7 (I34/A2), C2010.1, R2017.1
A3: A2001.8 (I39/A3), C2011.1, R2018.2
AMP_NON_IN_1: C2002.1, R2003.2, U2005.3 (+)
AMP_NON_IN_2: C2005.1, R2014.2, U2005.5 (+)
BAT+: BT2001.1 (+), J2003.1
COL_1: J2001.5, U2001.28 (GPA7)
COL_2: J2001.6, U2001.27 (GPA6)
COL_3: J2001.7, U2001.26 (GPA5)
COL_4: J2001.8, U2001.25 (GPA4)
COL_5: J2001.25, U2001.24 (GPA3)
COL_6: J2001.26, U2001.23 (GPA2)
COL_7: J2001.27, U2001.22 (GPA1)
COL_8: J2001.28, U2001.21 (GPA0)
COL_9: J2001.24, U2001.8 (GPB7)
COL_10: J2001.23, U2001.7 (GPB6)
COL_11: J2001.22, U2001.6 (GPB5)
COL_12: J2001.21, U2001.5 (GPB4)
COL_13: J2001.4, U2001.4 (GPB3)
COL_14: J2001.3, U2001.3 (GPB2)
COL_15: J2001.2, U2001.2 (GPB1)
COL_16: J2001.1, U2001.1 (GPB0)
COL_17: J2001.16, U2003.28 (GPA7)
COL_18: J2001.15, U2003.27 (GPA6)
COL_19: J2001.14, U2003.26 (GPA5)
COL_20: J2001.13, U2003.25 (GPA4)
COL_21: J2001.30, U2003.6 (GPB5)
COL_22: J2001.29, U2003.5 (GPB4)
COL_23: J2001.9, U2003.4 (GPB3)
COL_24: J2001.10, U2003.3 (GPB2)
COL_25: J2001.11, U2003.2 (GPB1)
COL_26: J2001.12, U2003.1 (GPB0)
GND: A2001.4 (GND), A2001.6 (DAC1/A1), C2001.2, C2002.2, C2003.2, C2004.2, C2005.2, C2006.2, C2007.2, C2008.2, C2009.2, C2010.2, C2011.2, C2012.2, C2013.2, J2001.32, J2002.3, JP2001.1 (A), R2001.2, R2002.2, R2004.2, R2005.2, R2006.2, R2007.2, R2008.2, R2009.2, R2010.2, R2011.2, R2012.2, R2013.2, R2015.2, R2016.2, U2001.10 (VSS), U2001.15 (A0), U2001.16 (A1), U2001.17 (A2), U2002.3 (VSS), U2002.14 (GND), U2003.10 (VSS), U2003.15 (A0), U2003.16 (A1), U2003.17 (A2), U2004.3 (VSS), U2004.14 (GND), U2005.4 (V-), U2006.1 (Vss)
GPIO_5: A2001.11 (SCK/IO5), U2001.12 (SCK), U2003.12 (SCK)
GPIO_12: A2001.24 (A11/IO12), U2001.11 (~CS)
GPIO_13: A2001.25 (A12/IO13), U2003.11 (~CS)
GPIO_14: A2001.19 (A6/IO14), U2002.1 (A0), U2004.1 (A0)
GPIO_15: A2001.21 (A8/IO15), U2002.15 (A2), U2004.15 (A2)
GPIO_18: A2001.12 (MOSI/IO18), U2001.13 (SI), U2003.13 (SI)
GPIO_19: A2001.13 (MISO/IO19), U2001.14 (SO), U2003.14 (SO)
GPIO_27: A2001.23 (A10/IO27), U2004.2 (EN)
GPIO_32: A2001.20 (A7/IO32), U2002.16 (A1), U2004.16 (A1)
GPIO_33: A2001.22 (A9/IO33), U2002.2 (EN)
unnamed: A2001.2 (3V3), C2012.1, F2001.1
unnamed: A2001.16 (IO21), JP2001.2 (B)
unnamed: C2007.1, U2004.9 (S8), U2006.2 (Vout)
unnamed: R2003.1, R2006.1, U2002.8 (D)
unnamed: R2014.1, R2016.1, U2004.8 (D)
unnamed: R2017.2, U2005.1, U2005.2 (-)
unnamed: R2018.1, U2005.6 (-), U2005.7
ROW_1: J2001.17, R2001.1, U2002.4 (S1)
ROW_2: J2001.18, R2002.1, U2002.5 (S2)
ROW_3: J2001.19, R2004.1, U2002.6 (S3)
ROW_4: J2001.20, R2005.1, U2002.7 (S4)
ROW_5: J2001.40, R2007.1, U2002.12 (S5)
ROW_6: J2001.39, R2008.1, U2002.11 (S6)
ROW_7: J2001.38, R2009.1, U2002.10 (S7)
ROW_8: J2001.37, R2010.1, U2002.9 (S8)
ROW_9: J2001.36, R2011.1, U2004.4 (S1)
ROW_10: J2001.35, R2012.1, U2004.5 (S2)
ROW_11: J2001.34, R2013.1, U2004.6 (S3)
ROW_12: J2001.33, R2015.1, U2004.7 (S4)
UART_RX: A2001.14 (RX/IO16), J2002.1
UART_TX: A2001.15 (TX/IO17), J2002.2

Notes on the sheet:
Battery
Logic Schematic
Note: The OPA2333xxD is SMD and is a dual op-amp package. In its datasheet, one of its applications is temperature measurements which is neat.
Note: The MCP1525 is a type of regulator that outputs 2.5V that can be used for two-point calibration.
Note: +BATT and -BATT are connected to the MCU; the battery JST would be connected to the JST on the MCU.
LionStride
Microcontroller
Multiplexers
Jumper represents a possible connectiom, where no connection is for temperature and a connection is pressure.
IO-expanders
Buffers
External header connections
