3pnguyen/lionstride-inventeam-2026/Prototype Schematics/Prototype Schematic (TIA)/inventeam_proto_schematics_tia/Thermistor Matrix Schematic.kicad_sch

## KiCad design Prototype Schematics/Prototype Schematic (TIA)/inventeam_proto_schematics_tia/Thermistor Matrix Schematic.kicad_sch (2026-03-04)

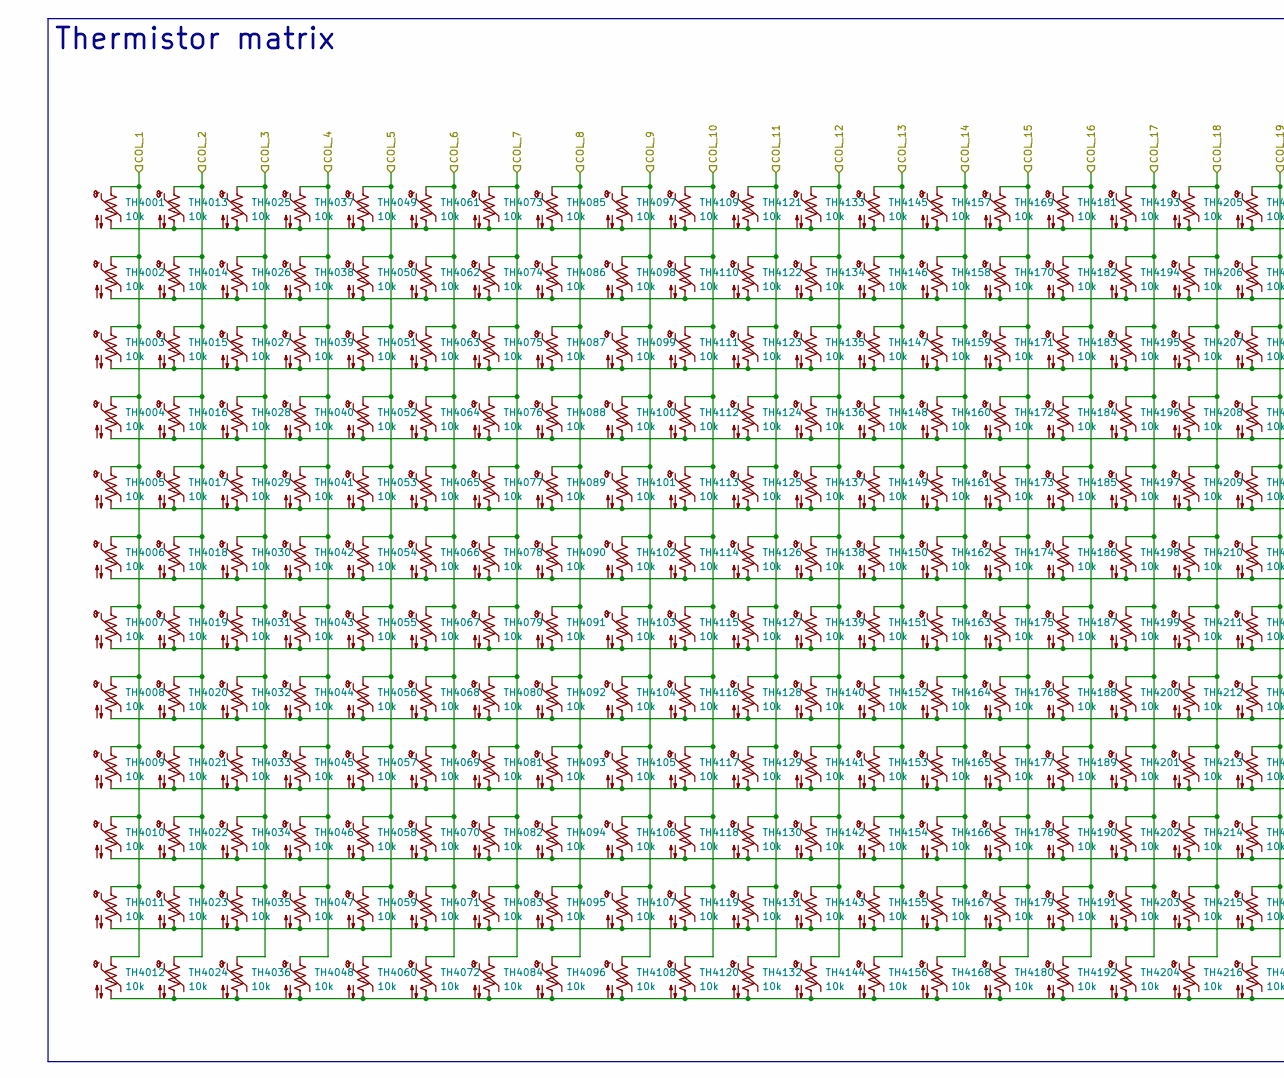
[picture p33: schematic Thermistor Matrix Schematic.kicad_sch, part in row 1, column 1]

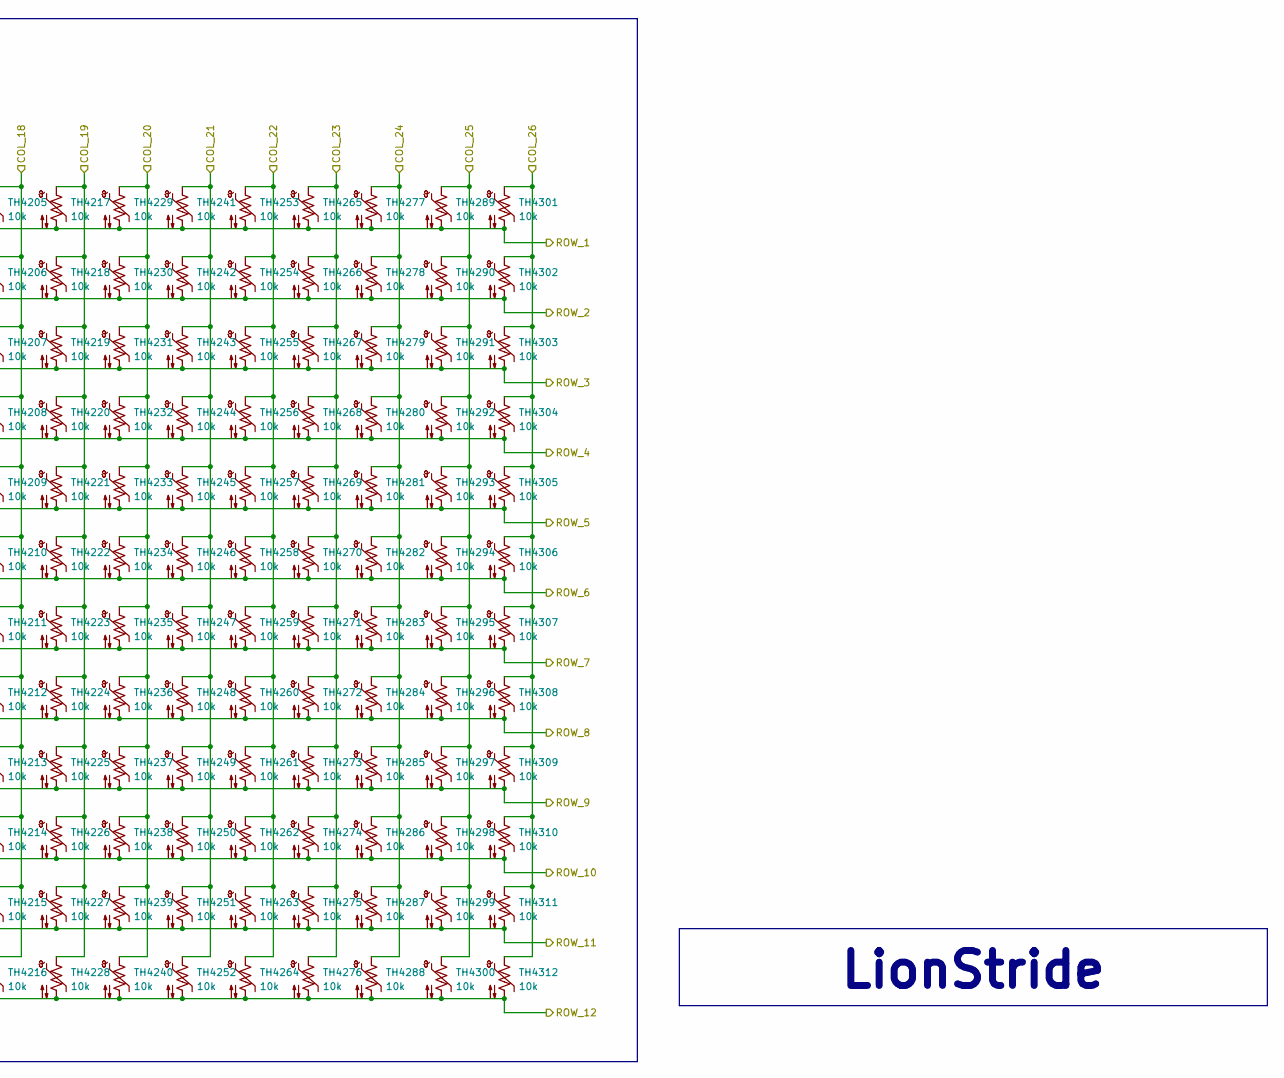
[picture p34: schematic Thermistor Matrix Schematic.kicad_sch, part in row 1, column 2]

Parts:
TH4001, TH4002, TH4003, TH4004, TH4005, TH4006, TH4007, TH4008, TH4009, TH4010, TH4011, TH4012, TH4013, TH4014, TH4015, TH4016, TH4017, TH4018, TH4019, TH4020, TH4021, TH4022, TH4023, TH4024, TH4025, TH4026, TH4027, TH4028, TH4029, TH4030, TH4031, TH4032, TH4033, TH4034, TH4035, TH4036, TH4037, TH4038, TH4039, TH4040, TH4041, TH4042, TH4043, TH4044, TH4045, TH4046, TH4047, TH4048, TH4049, TH4050, TH4051, TH4052, TH4053, TH4054, TH4055, TH4056, TH4057, TH4058, TH4059, TH4060, TH4061, TH4062, TH4063, TH4064, TH4065, TH4066, TH4067, TH4068, TH4069, TH4070, TH4071, TH4072, TH4073, TH4074, TH4075, TH4076, TH4077, TH4078, TH4079, TH4080, TH4081, TH4082, TH4083, TH4084, TH4085, TH4086, TH4087, TH4088, TH4089, TH4090, TH4091, TH4092, TH4093, TH4094, TH4095, TH4096, TH4097, TH4098, TH4099, TH4100, TH4101, TH4102, TH4103, TH4104, TH4105, TH4106, TH4107, TH4108, TH4109, TH4110, TH4111, TH4112, TH4113, TH4114, TH4115, TH4116, TH4117, TH4118, TH4119, TH4120, TH4121, TH4122, TH4123, TH4124, TH4125, TH4126, TH4127, TH4128, TH4129, TH4130, TH4131, TH4132, TH4133, TH4134, TH4135, TH4136, TH4137, TH4138, TH4139, TH4140, TH4141, TH4142, TH4143, TH4144, TH4145, TH4146, TH4147, TH4148, TH4149, TH4150, TH4151, TH4152, TH4153, TH4154, TH4155, TH4156, TH4157, TH4158, TH4159, TH4160, TH4161, TH4162, TH4163, TH4164, TH4165, TH4166, TH4167, TH4168, TH4169, TH4170, TH4171, TH4172, TH4173, TH4174, TH4175, TH4176, TH4177, TH4178, TH4179, TH4180, TH4181, TH4182, TH4183, TH4184, TH4185, TH4186, TH4187, TH4188, TH4189, TH4190, TH4191, TH4192, TH4193, TH4194, TH4195, TH4196, TH4197, TH4198, TH4199, TH4200, TH4201, TH4202, TH4203, TH4204, TH4205, TH4206, TH4207, TH4208, TH4209, TH4210, TH4211, TH4212, TH4213, TH4214, TH4215, TH4216, TH4217, TH4218, TH4219, TH4220, TH4221, TH4222, TH4223, TH4224, TH4225, TH4226, TH4227, TH4228, TH4229, TH4230, TH4231, TH4232, TH4233, TH4234, TH4235, TH4236, TH4237, TH4238, TH4239, TH4240, TH4241, TH4242, TH4243, TH4244, TH4245, TH4246, TH4247, TH4248, TH4249, TH4250, TH4251, TH4252, TH4253, TH4254, TH4255, TH4256, TH4257, TH4258, TH4259, TH4260, TH4261, TH4262, TH4263, TH4264, TH4265, TH4266, TH4267, TH4268, TH4269, TH4270, TH4271, TH4272, TH4273, TH4274, TH4275, TH4276, TH4277, TH4278, TH4279, TH4280, TH4281, TH4282, TH4283, TH4284, TH4285, TH4286, TH4287, TH4288, TH4289, TH4290, TH4291, TH4292, TH4293, TH4294, TH4295, TH4296, TH4297, TH4298, TH4299, TH4300, TH4301, TH4302, TH4303, TH4304, TH4305, TH4306, TH4307, TH4308, TH4309, TH4310, TH4311, TH4312: 10k

Connections:
COL_1: TH4001.1, TH4002.1, TH4003.1, TH4004.1, TH4005.1, TH4006.1, TH4007.1, TH4008.1, TH4009.1, TH4010.1, TH4011.1, TH4012.1
COL_2: TH4013.1, TH4014.1, TH4015.1, TH4016.1, TH4017.1, TH4018.1, TH4019.1, TH4020.1, TH4021.1, TH4022.1, TH4023.1, TH4024.1
COL_3: TH4025.1, TH4026.1, TH4027.1, TH4028.1, TH4029.1, TH4030.1, TH4031.1, TH4032.1, TH4033.1, TH4034.1, TH4035.1, TH4036.1
COL_4: TH4037.1, TH4038.1, TH4039.1, TH4040.1, TH4041.1, TH4042.1, TH4043.1, TH4044.1, TH4045.1, TH4046.1, TH4047.1, TH4048.1
COL_5: TH4049.1, TH4050.1, TH4051.1, TH4052.1, TH4053.1, TH4054.1, TH4055.1, TH4056.1, TH4057.1, TH4058.1, TH4059.1, TH4060.1
COL_6: TH4061.1, TH4062.1, TH4063.1, TH4064.1, TH4065.1, TH4066.1, TH4067.1, TH4068.1, TH4069.1, TH4070.1, TH4071.1, TH4072.1
COL_7: TH4073.1, TH4074.1, TH4075.1, TH4076.1, TH4077.1, TH4078.1, TH4079.1, TH4080.1, TH4081.1, TH4082.1, TH4083.1, TH4084.1
COL_8: TH4085.1, TH4086.1, TH4087.1, TH4088.1, TH4089.1, TH4090.1, TH4091.1, TH4092.1, TH4093.1, TH4094.1, TH4095.1, TH4096.1
COL_9: TH4097.1, TH4098.1, TH4099.1, TH4100.1, TH4101.1, TH4102.1, TH4103.1, TH4104.1, TH4105.1, TH4106.1, TH4107.1, TH4108.1
COL_10: TH4109.1, TH4110.1, TH4111.1, TH4112.1, TH4113.1, TH4114.1, TH4115.1, TH4116.1, TH4117.1, TH4118.1, TH4119.1, TH4120.1
COL_11: TH4121.1, TH4122.1, TH4123.1, TH4124.1, TH4125.1, TH4126.1, TH4127.1, TH4128.1, TH4129.1, TH4130.1, TH4131.1, TH4132.1
COL_12: TH4133.1, TH4134.1, TH4135.1, TH4136.1, TH4137.1, TH4138.1, TH4139.1, TH4140.1, TH4141.1, TH4142.1, TH4143.1, TH4144.1
COL_13: TH4145.1, TH4146.1, TH4147.1, TH4148.1, TH4149.1, TH4150.1, TH4151.1, TH4152.1, TH4153.1, TH4154.1, TH4155.1, TH4156.1
COL_14: TH4157.1, TH4158.1, TH4159.1, TH4160.1, TH4161.1, TH4162.1, TH4163.1, TH4164.1, TH4165.1, TH4166.1, TH4167.1, TH4168.1
COL_15: TH4169.1, TH4170.1, TH4171.1, TH4172.1, TH4173.1, TH4174.1, TH4175.1, TH4176.1, TH4177.1, TH4178.1, TH4179.1, TH4180.1
COL_16: TH4181.1, TH4182.1, TH4183.1, TH4184.1, TH4185.1, TH4186.1, TH4187.1, TH4188.1, TH4189.1, TH4190.1, TH4191.1, TH4192.1
COL_17: TH4193.1, TH4194.1, TH4195.1, TH4196.1, TH4197.1, TH4198.1, TH4199.1, TH4200.1, TH4201.1, TH4202.1, TH4203.1, TH4204.1
COL_18: TH4205.1, TH4206.1, TH4207.1, TH4208.1, TH4209.1, TH4210.1, TH4211.1, TH4212.1, TH4213.1, TH4214.1, TH4215.1, TH4216.1
COL_19: TH4217.1, TH4218.1, TH4219.1, TH4220.1, TH4221.1, TH4222.1, TH4223.1, TH4224.1, TH4225.1, TH4226.1, TH4227.1, TH4228.1
COL_20: TH4229.1, TH4230.1, TH4231.1, TH4232.1, TH4233.1, TH4234.1, TH4235.1, TH4236.1, TH4237.1, TH4238.1, TH4239.1, TH4240.1
COL_21: TH4241.1, TH4242.1, TH4243.1, TH4244.1, TH4245.1, TH4246.1, TH4247.1, TH4248.1, TH4249.1, TH4250.1, TH4251.1, TH4252.1
COL_22: TH4253.1, TH4254.1, TH4255.1, TH4256.1, TH4257.1, TH4258.1, TH4259.1, TH4260.1, TH4261.1, TH4262.1, TH4263.1, TH4264.1
COL_23: TH4265.1, TH4266.1, TH4267.1, TH4268.1, TH4269.1, TH4270.1, TH4271.1, TH4272.1, TH4273.1, TH4274.1, TH4275.1, TH4276.1
COL_24: TH4277.1, TH4278.1, TH4279.1, TH4280.1, TH4281.1, TH4282.1, TH4283.1, TH4284.1, TH4285.1, TH4286.1, TH4287.1, TH4288.1
COL_25: TH4289.1, TH4290.1, TH4291.1, TH4292.1, TH4293.1, TH4294.1, TH4295.1, TH4296.1, TH4297.1, TH4298.1, TH4299.1, TH4300.1
COL_26: TH4301.1, TH4302.1, TH4303.1, TH4304.1, TH4305.1, TH4306.1, TH4307.1, TH4308.1, TH4309.1, TH4310.1, TH4311.1, TH4312.1
ROW_1: TH4001.2, TH4013.2, TH4025.2, TH4037.2, TH4049.2, TH4061.2, TH4073.2, TH4085.2, TH4097.2, TH4109.2, TH4121.2, TH4133.2, TH4145.2, TH4157.2, TH4169.2, TH4181.2, TH4193.2, TH4205.2, TH4217.2, TH4229.2, TH4241.2, TH4253.2, TH4265.2, TH4277.2, TH4289.2, TH4301.2
ROW_2: TH4002.2, TH4014.2, TH4026.2, TH4038.2, TH4050.2, TH4062.2, TH4074.2, TH4086.2, TH4098.2, TH4110.2, TH4122.2, TH4134.2, TH4146.2, TH4158.2, TH4170.2, TH4182.2, TH4194.2, TH4206.2, TH4218.2, TH4230.2, TH4242.2, TH4254.2, TH4266.2, TH4278.2, TH4290.2, TH4302.2
ROW_3: TH4003.2, TH4015.2, TH4027.2, TH4039.2, TH4051.2, TH4063.2, TH4075.2, TH4087.2, TH4099.2, TH4111.2, TH4123.2, TH4135.2, TH4147.2, TH4159.2, TH4171.2, TH4183.2, TH4195.2, TH4207.2, TH4219.2, TH4231.2, TH4243.2, TH4255.2, TH4267.2, TH4279.2, TH4291.2, TH4303.2
ROW_4: TH4004.2, TH4016.2, TH4028.2, TH4040.2, TH4052.2, TH4064.2, TH4076.2, TH4088.2, TH4100.2, TH4112.2, TH4124.2, TH4136.2, TH4148.2, TH4160.2, TH4172.2, TH4184.2, TH4196.2, TH4208.2, TH4220.2, TH4232.2, TH4244.2, TH4256.2, TH4268.2, TH4280.2, TH4292.2, TH4304.2
ROW_5: TH4005.2, TH4017.2, TH4029.2, TH4041.2, TH4053.2, TH4065.2, TH4077.2, TH4089.2, TH4101.2, TH4113.2, TH4125.2, TH4137.2, TH4149.2, TH4161.2, TH4173.2, TH4185.2, TH4197.2, TH4209.2, TH4221.2, TH4233.2, TH4245.2, TH4257.2, TH4269.2, TH4281.2, TH4293.2, TH4305.2
ROW_6: TH4006.2, TH4018.2, TH4030.2, TH4042.2, TH4054.2, TH4066.2, TH4078.2, TH4090.2, TH4102.2, TH4114.2, TH4126.2, TH4138.2, TH4150.2, TH4162.2, TH4174.2, TH4186.2, TH4198.2, TH4210.2, TH4222.2, TH4234.2, TH4246.2, TH4258.2, TH4270.2, TH4282.2, TH4294.2, TH4306.2
ROW_7: TH4007.2, TH4019.2, TH4031.2, TH4043.2, TH4055.2, TH4067.2, TH4079.2, TH4091.2, TH4103.2, TH4115.2, TH4127.2, TH4139.2, TH4151.2, TH4163.2, TH4175.2, TH4187.2, TH4199.2, TH4211.2, TH4223.2, TH4235.2, TH4247.2, TH4259.2, TH4271.2, TH4283.2, TH4295.2, TH4307.2
ROW_8: TH4008.2, TH4020.2, TH4032.2, TH4044.2, TH4056.2, TH4068.2, TH4080.2, TH4092.2, TH4104.2, TH4116.2, TH4128.2, TH4140.2, TH4152.2, TH4164.2, TH4176.2, TH4188.2, TH4200.2, TH4212.2, TH4224.2, TH4236.2, TH4248.2, TH4260.2, TH4272.2, TH4284.2, TH4296.2, TH4308.2
ROW_9: TH4009.2, TH4021.2, TH4033.2, TH4045.2, TH4057.2, TH4069.2, TH4081.2, TH4093.2, TH4105.2, TH4117.2, TH4129.2, TH4141.2, TH4153.2, TH4165.2, TH4177.2, TH4189.2, TH4201.2, TH4213.2, TH4225.2, TH4237.2, TH4249.2, TH4261.2, TH4273.2, TH4285.2, TH4297.2, TH4309.2
ROW_10: TH4010.2, TH4022.2, TH4034.2, TH4046.2, TH4058.2, TH4070.2, TH4082.2, TH4094.2, TH4106.2, TH4118.2, TH4130.2, TH4142.2, TH4154.2, TH4166.2, TH4178.2, TH4190.2, TH4202.2, TH4214.2, TH4226.2, TH4238.2, TH4250.2, TH4262.2, TH4274.2, TH4286.2, TH4298.2, TH4310.2
ROW_11: TH4011.2, TH4023.2, TH4035.2, TH4047.2, TH4059.2, TH4071.2, TH4083.2, TH4095.2, TH4107.2, TH4119.2, TH4131.2, TH4143.2, TH4155.2, TH4167.2, TH4179.2, TH4191.2, TH4203.2, TH4215.2, TH4227.2, TH4239.2, TH4251.2, TH4263.2, TH4275.2, TH4287.2, TH4299.2, TH4311.2
ROW_12: TH4012.2, TH4024.2, TH4036.2, TH4048.2, TH4060.2, TH4072.2, TH4084.2, TH4096.2, TH4108.2, TH4120.2, TH4132.2, TH4144.2, TH4156.2, TH4168.2, TH4180.2, TH4192.2, TH4204.2, TH4216.2, TH4228.2, TH4240.2, TH4252.2, TH4264.2, TH4276.2, TH4288.2, TH4300.2, TH4312.2

Notes on the sheet:
LionStride
Thermistor matrix
